VanceVagell/kv4p-ht/website-src/img/v1.7b-harmonics.jpg

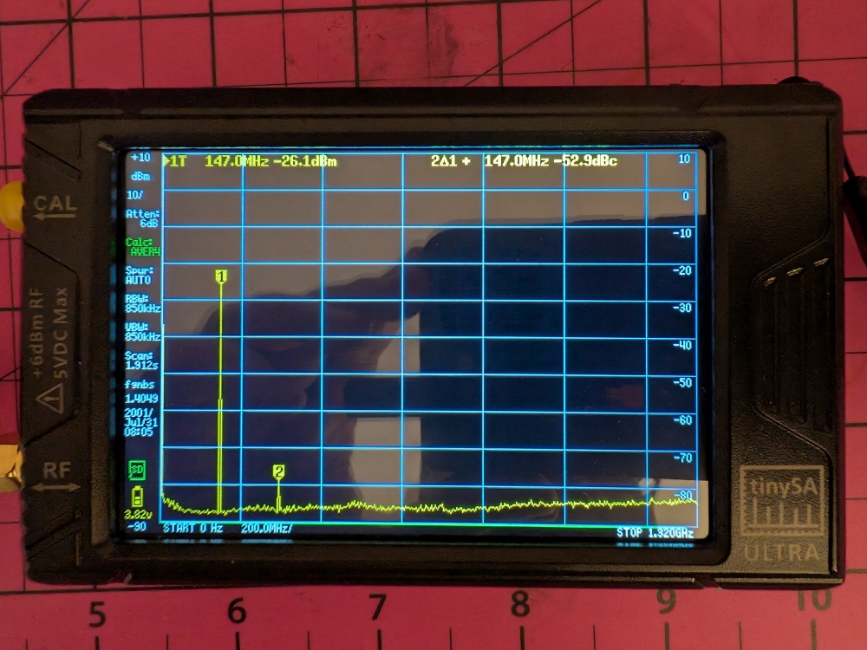
website-src/img/v1.7b-harmonics.jpg
