VanceVagell/kv4p-ht/3d-print-case/Cases for 2.x PCB/Sleek (official)/Sleek KV4P HT case (for PCB 2.x) - logo inlay.stl

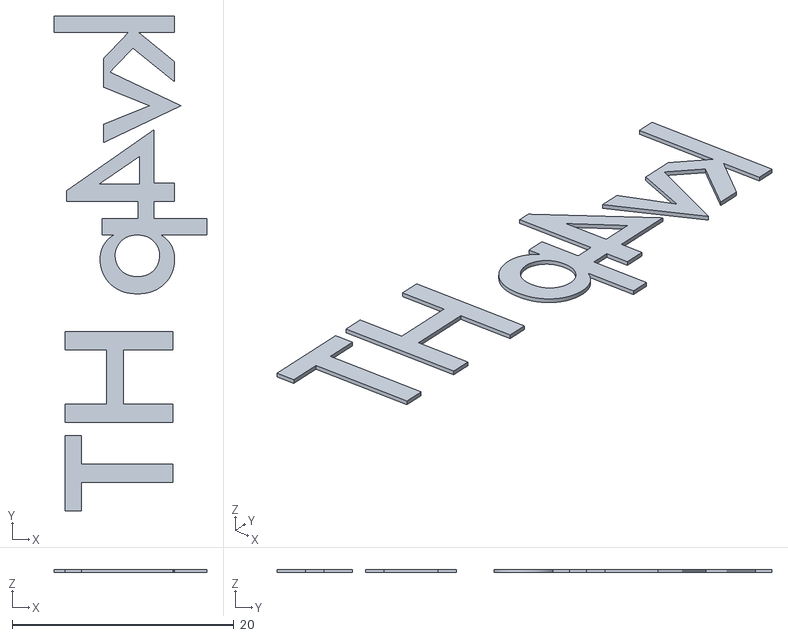
[picture p22: CAD file, 2026-09-27]
3d-print-case/Cases for 2.x PCB/Sleek (official)/Sleek KV4P HT case (for PCB 2.x) - logo inlay.stl
13.8 x 44.6 x 0.306
