VanceVagell/kv4p-ht/3d-print-case/Cases for 1.x PCB/alternate case designs/PCB slide-in case with stand/KV4P HT Stand.stl

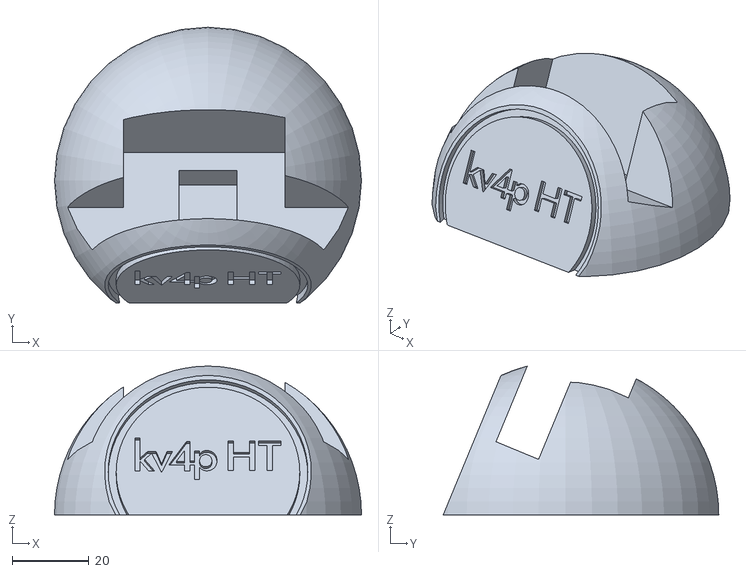
[picture p23: CAD file, 2024-06-17]
3d-print-case/Cases for 1.x PCB/alternate case designs/PCB slide-in case with stand/KV4P HT Stand.stl
80.0 x 71.8 x 38.7
