VanceVagell/kv4p-ht/3d-print-case/Cases for 2.x PCB/Community designs/KB9VQQ Design/Thin Case/kv4p-ThinCase-Body.stl

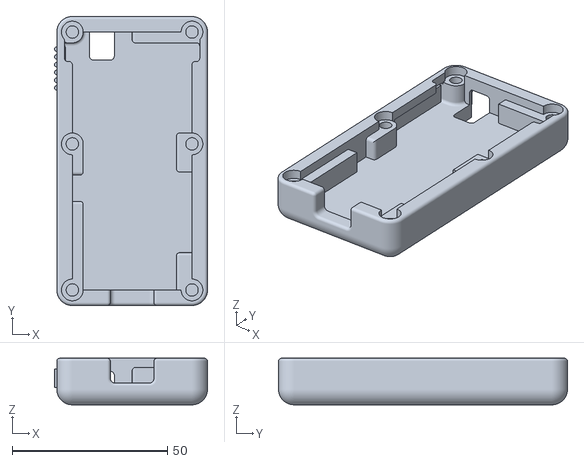
[picture p24: CAD file, 2025-10-06]
3d-print-case/Cases for 2.x PCB/Community designs/KB9VQQ Design/Thin Case/kv4p-ThinCase-Body.stl
49.2 x 93.0 x 15.0
