VanceVagell/kv4p-ht/3d-print-case/Cases for 2.x PCB/Rugged (official)/Rugged KV4P HT case (for PCB 2.x) - back.stl

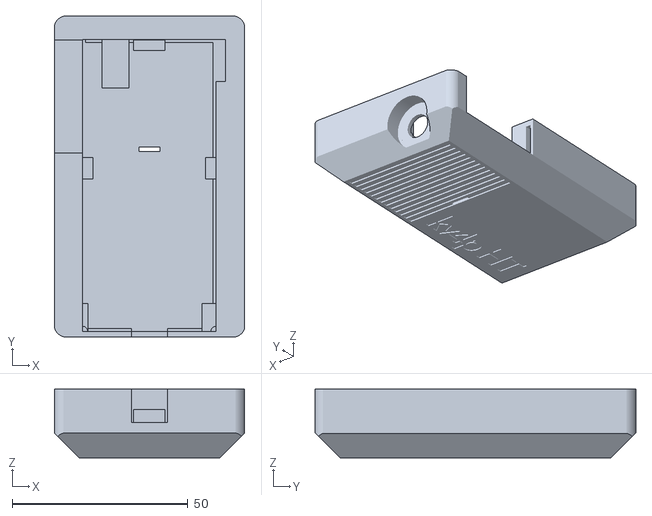
[picture p25: CAD file, 2026-09-27]
3d-print-case/Cases for 2.x PCB/Rugged (official)/Rugged KV4P HT case (for PCB 2.x) - back.stl
54.0 x 91.1 x 19.5
