VanceVagell/kv4p-ht/android-src/KV4PHT/app/src/main/java/com/vagell/kv4pht/radio/RadioAudioService.java

/*
kv4p HT (see http://kv4p.com)
Copyright (C) 2024 Vance Vagell

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
You should have received a copy of the GNU General Public License
along with this program.  If not, see <http://www.gnu.org/licenses/>.
*/

package com.vagell.kv4pht.radio;

import android.Manifest;
import android.app.Notification;
import android.app.NotificationChannel;
import android.app.NotificationManager;
import android.app.PendingIntent;
import android.app.Service;
import android.content.Context;
import android.content.Intent;
import android.content.pm.PackageManager;
import android.content.pm.ServiceInfo;
import android.hardware.usb.UsbDevice;
import android.hardware.usb.UsbDeviceConnection;
import android.hardware.usb.UsbManager;
import android.media.AudioAttributes;
import android.media.AudioFocusRequest;
import android.media.AudioFormat;
import android.media.AudioManager;
import android.media.AudioRecord;
import android.media.AudioTrack;
import android.media.MediaRecorder;
import android.os.Binder;
import android.os.Build;
import android.os.Bundle;
import android.os.Handler;
import android.os.IBinder;
import android.os.Looper;
import android.os.PowerManager;
import android.util.Log;
import androidx.annotation.NonNull;
import androidx.annotation.RequiresApi;
import androidx.annotation.RequiresPermission;
import androidx.core.app.NotificationCompat;
import androidx.lifecycle.LiveData;
import com.google.android.gms.common.ConnectionResult;
import com.google.android.gms.common.GoogleApiAvailability;
import com.google.android.gms.location.FusedLocationProviderClient;
import com.google.android.gms.location.LocationServices;
import com.google.android.gms.location.Priority;
import com.google.android.gms.tasks.CancellationToken;
import com.google.android.gms.tasks.CancellationTokenSource;
import com.hoho.android.usbserial.driver.UsbSerialDriver;
import com.hoho.android.usbserial.driver.UsbSerialPort;
import com.hoho.android.usbserial.driver.UsbSerialProber;
import com.vagell.kv4pht.BuildConfig;
import com.vagell.kv4pht.R;
import io.github.dkaukov.aprs.AprsController;
import io.github.dkaukov.aprs.BeaconData;
import io.github.dkaukov.aprs.AprsEvent;
import io.github.dkaukov.aprs.AprsIsClient;
import io.github.dkaukov.aprs.AprsSource;
import com.vagell.kv4pht.ui.APRSIconType;
import io.github.dkaukov.aprs.parser.APRSPacket;
import io.github.dkaukov.aprs.parser.Digipeater;
import io.github.dkaukov.aprs.parser.Parser;
import com.vagell.kv4pht.data.ChannelMemory;
import com.vagell.kv4pht.data.AprsFeedRepository;
import com.vagell.kv4pht.data.AprsFeedRow;
import com.vagell.kv4pht.data.AppDatabase;
import com.vagell.kv4pht.data.RoomAprsRepository;
import com.vagell.kv4pht.firmware.FirmwareUtils;
import com.vagell.kv4pht.javAX25.ax25.Packet;
import com.vagell.kv4pht.radio.Protocol.KissParser;
import com.vagell.kv4pht.radio.Protocol.RcvCommand;
import com.vagell.kv4pht.radio.Protocol.WindowUpdate;
import com.vagell.kv4pht.ui.MainActivity;
import com.vagell.kv4pht.ui.ToneHelper;
import io.github.dkaukov.codec2.Codec2;
import lombok.Getter;
import lombok.Setter;
import java.nio.ByteBuffer;
import java.nio.charset.StandardCharsets;
import java.util.Collections;
import java.util.List;
import java.util.Locale;
import java.util.Optional;
import java.util.concurrent.Executors;
import java.util.concurrent.ExecutorService;
import java.util.concurrent.ScheduledExecutorService;
import java.util.concurrent.TimeUnit;
import java.util.concurrent.atomic.AtomicInteger;
import java.util.concurrent.atomic.AtomicReference;

/**
 * Background service that manages the connection to the ESP32 (to control the radio), and
 * handles playing back any audio received from the radio. This frees up the rest of the
 * application to focus primarily on the setup flows and UI, and ensures that the radio audio
 * continues to play even if the phone's screen is off or the user starts another app.
 */
public class RadioAudioService extends Service {
    private static final String MEGAHERTZ = " MHz";
    private static final String MEMORY_FREQUENCY_SUFFIX = MEGAHERTZ + ")";
    private static final String SIMPLEX_PREFIX = "Simplex ";
    private static final String CURRENT_FREQUENCY = "Current";
    private static final String NOTIFICATION_CHANNEL_ID = "KV4P_HT_RADIO_AUDIO";

    // === Constants ===
    private static final String TAG = RadioAudioService.class.getSimpleName();
    private static final String FIRMWARE_TAG = "firmware";
    private static final String APRS_TOCALL = "APKVPA";
    private static final String ACTION_USB_PERMISSION = "com.vagell.kv4pht.USB_PERMISSION";
    private static final int RUNAWAY_TX_TIMEOUT_SEC = 180;
    // Intents this Activity can handle besides the one that starts it in default mode.
    public static final String INTENT_OPEN_CHAT = "com.vagell.kv4pht.OPEN_CHAT_ACTION";
    public static final String ACTION_STOP_SERVICE = "com.vagell.kv4pht.STOP_RADIO_SERVICE";
    public static final String ACTION_SERVICE_STOPPING = "com.vagell.kv4pht.SERVICE_STOPPING";


    // === USB Device Matching ===
    private static final int[] ESP32_VENDOR_IDS = {4292, 6790};
    private static final int[] ESP32_PRODUCT_IDS = {60000, 29987};

    // === Audio Constants ===
    public static final int AUDIO_SAMPLE_RATE = 16000;
    private static final int RX_AUDIO_CHANNEL_CONFIG = AudioFormat.CHANNEL_OUT_MONO;
    private static final int RX_AUDIO_FORMAT = AudioFormat.ENCODING_PCM_16BIT;
    public static final int AUDIO_FRAME_SAMPLES = 249; // One 128-byte mono IMA ADPCM audio block at 16kHz
    public static final int AUDIO_FRAME_BYTES = ImaAdpcm.encodedSize(AUDIO_FRAME_SAMPLES);
    private static final int RX_AUDIO_MIN_BUFFER_SIZE =
            Math.max(AudioTrack.getMinBufferSize(
                    AUDIO_SAMPLE_RATE,
                    RX_AUDIO_CHANNEL_CONFIG,
                    RX_AUDIO_FORMAT),
                    AUDIO_FRAME_SAMPLES * 2);

    // === APRS Constants ===
    public static final int APRS_POSITION_EXACT = 0;
    public static final int APRS_POSITION_APPROX = 1;
    public static final int APRS_BEACON_MINS = 5;
    public static final String MESSAGE_NOTIFICATION_CHANNEL_ID = "aprs_message_notifications";
    public static final int MESSAGE_NOTIFICATION_TO_YOU_ID = 0;
    public static final List<Digipeater> DEFAULT_DIGIPEATERS = List.of(new Digipeater("WIDE1-1"), new Digipeater("WIDE2-1"));
    private static final long SCAN_SQUELCHED_ADVANCE_DELAY_MS = 250L;

    // === Used for the persistent notification ===
    private PowerManager.WakeLock wakeLock;
    private static final int SERVICE_ID = 1;

    // These will be overwritten by user settings
    @Setter
    private float min2mTxFreq = 144.0f;
    @Setter
    private float max2mTxFreq = 148.0f;
    @Setter
    private float min70cmTxFreq = 420.0f;
    @Setter
    private float max70cmTxFreq = 450.0f;

    @Setter
    private float minTxFreq = min2mTxFreq;
    @Setter
    private float maxTxFreq = max2mTxFreq;

    @Setter
    private APRSIconType aprsPositionIcon = APRSIconType.T_PHONE;

    public enum RadioModuleType {UNKNOWN, VHF, UHF}

    // === Audio / 4-bit IMA ADPCM Handling ===
    private final short[] pcm16 = new short[AUDIO_FRAME_SAMPLES];
    private AudioTrack audioTrack;
    private float audioTrackVolume = 0.0f;
    private AudioFocusRequest audioFocusRequest;
    private boolean hasAudioFocus = false;
    private final byte[] txAudioFrame = new byte[AUDIO_FRAME_BYTES];
    private final ImaAdpcm.Encoder txAudioEncoder = new ImaAdpcm.Encoder();
    private Codec2 codec2;
    private boolean freeDv2400bEnabled;
    private final short[] codec2TxPcm = new short[Codec2.PCM_SAMPLES];
    private final short[] codec2RxPcm = new short[Codec2.PCM_SAMPLES];
    private final short[] codec2PlaybackPcm = new short[Codec2.PCM_SAMPLES * 2];
    private final byte[] codec2Frame = new byte[Codec2.FRAME_BYTES];
    private int codec2TxSamples;
    private boolean codec2HasPendingInput;
    private short codec2PendingInput;
    private final AtomicReference<AudioRecord> audioRecord = new AtomicReference<>();
    private volatile boolean voiceCaptureActive;
    private final AtomicInteger voiceCaptureSession = new AtomicInteger();
    private static final int TX_AUDIO_MIN_BUFFER_SIZE = Math.max(
            AudioRecord.getMinBufferSize(AUDIO_SAMPLE_RATE, AudioFormat.CHANNEL_IN_MONO,
                    AudioFormat.ENCODING_PCM_16BIT), AUDIO_FRAME_SAMPLES * 2);

    // === USB / Serial ===
    private UsbManager usbManager;
    private RadioTransport activeTransport;
    private boolean usbPermissionRequestPending = false;
    @Getter
    private Protocol.Sender hostToEsp32;
    @Getter
    private final RadioModuleController radioModule = new RadioModuleController();
    private final KissParser esp32DataStreamParser = new KissParser(this::handleParsedCommand, this::handleEsp32Ax25Packet);
    private int usbConnectAttemptSeq = 0;
    private int activeUsbConnectAttemptId = 0;

    // === APRS State ===
    private String aprsBeaconFrequency = CURRENT_FREQUENCY;
    // Confined to the ordered APRS worker while submitting one app-scheduled beacon.
    private Float aprsBeaconTxOverrideMhz;
    @Getter
    @Setter
    private int aprsPositionAccuracy = APRS_POSITION_EXACT;
    private AprsIsClient aprsIsClient;
    private boolean aprsIgateEnabled;
    private boolean aprsIsDisplayEnabled;

    // === Protocol Handshake ===
    private static final int HELLO_TIMEOUT_MS = 60000;
    private int handshakeSeq = 0;
    private int activeHandshakeId = 0;
    private boolean waitingForHello = false;
    private Runnable helloTimeoutRunnable;

    // === Radio State ===
    @Getter
    private @NonNull RadioMode mode = RadioMode.STARTUP;
    private @NonNull String callsign = "";
    @Getter
    private @NonNull String activeFrequencyStr = "";
    private int activeMemoryId = -1;
    private int scanBaseSquelch = -1;
    private static final int DEFAULT_SCAN_SQUELCH = 7;
    private Runnable pendingScanAdvance;
    private int pendingScanAdvanceMemoryId = -1;
    private MicGainBoost micGainBoost = MicGainBoost.NONE;

    // === Android Components ===
    private final IBinder binder = new RadioBinder();
    private static final RadioAudioServiceCallbacks NO_OP_CALLBACKS = new RadioAudioServiceCallbacks() {};
    @Setter
    @Getter
    private @NonNull RadioAudioServiceCallbacks callbacks = NO_OP_CALLBACKS;
    private final Handler handler = new Handler(Looper.getMainLooper());
    private static final long CONNECT_RETRY_PERIOD_MS = 500L;
    private final ConnectionController connectionController =
        new ConnectionController(handler, CONNECT_RETRY_PERIOD_MS, this::reconcileConnections);
    private boolean radioMissingNotified = false;
    private Runnable txTimeoutHandler;
    private LiveData<List<ChannelMemory>> channelMemoriesLiveData = null;
    private ScheduledExecutorService aprsExecutor;
    private volatile boolean aprsBeaconPosition;
    // Main-handler-owned scheduling preserves GPS and alternate-frequency beaconing.
    private final AprsBeaconSchedule aprsBeaconSchedule = new AprsBeaconSchedule(APRS_BEACON_MINS * 60_000L);
    private AprsController aprsController;
    private AprsFeedRepository aprsFeedRepository;

    /**
     * Class used for the client Binder. This service always runs in the same process as its clients.
     */
    public class RadioBinder extends Binder {
        public RadioAudioService getService() {
            // Return this instance of RadioService so clients can call public methods.
            return RadioAudioService.this;
        }
    }

    /**
     * Callbacks for the activity to implement, so it can be notified of various events.
     */
    public interface RadioAudioServiceCallbacks {
        default void radioMissing() {}
        default void radioConnected() {}
        default void hideSnackBar() {}
        default void radioModuleHandshake() {}
        default void radioModuleNotFound() {}
        default void audioTrackCreated() {}
        default void startingAprsBeacon(String frequencyStr) {}
        default void scannedToMemory(int memoryId) {}
        default void tunedToFreq(String frequencyStr) {}
        default void outdatedFirmware(int firmwareVer) {}
        default void initialDeviceStateReceived() {}
        default void radioConfigChanged() {}
        default void missingFirmware() {}
        default void txStarted() {}
        default void txEnded() {}
        default void moduleStateChanged(boolean txActive, boolean squelched) {}
        default void freeDvModeChanged(boolean enabled) {}
        default void chatError(String text) {}
        default void sMeterUpdate(int value) {}
        default void sentAprsBeacon(double latitude, double longitude, String frequencyStr, boolean wasSwitch) {}
        default void unknownLocation() {}
        default void forcedPttStart() {}
        default void forcedPttEnd() {}
        default void setRadioType(RadioModuleType ratioType) {}
        default void showNotification(String notificationChannelId, int notificationTypeId, String title, String message, String tapIntentName) {}
    }

    @Override
    public IBinder onBind(Intent intent) {
        Bundle bundle = intent.getExtras();
        if (null == bundle) {
            Log.d(TAG, "Warning: RadioAudioService started without parameters, likely in a bad state.");
            return binder;
        }

        // Retrieve necessary parameters from the intent.
        setCallsign(Optional.ofNullable(bundle.getString("callsign")).orElse(""));
        if (bundle.containsKey("squelch")) {
            radioModule.seedDesiredSquelch(bundle.getInt("squelch"));
        }
        activeMemoryId = bundle.getInt("activeMemoryId");
        activeFrequencyStr = Optional.ofNullable(bundle.getString("activeFrequencyStr")).orElse("");
        return binder;
    }

    public void setMicGainBoost(String micGainBoost) {
        this.micGainBoost = MicGainBoost.parse(micGainBoost);
    }

    public void setAprsBeaconPosition(boolean enabled) {
        aprsBeaconPosition = enabled;
        handler.post(() -> aprsBeaconSchedule.setEnabled(enabled));
    }

    public void setAprsBeaconFrequency(String frequency) {
        this.aprsBeaconFrequency = frequency;
    }

    public void setDigipeatPackets(boolean enabled) {
        executeAprs(() -> aprsController.setDigipeatingEnabled(enabled));
    }

    public void setAprsIgateEnabled(boolean enabled) {
        aprsIgateEnabled = enabled;
        executeAprs(() -> aprsController.setIgateEnabled(enabled));
        updateAprsIsConnection();
    }

    public void setAprsIsDisplayEnabled(boolean enabled) {
        aprsIsDisplayEnabled = enabled;
        AprsIsClient client = aprsIsClient;
        if (client != null) client.setReceiveEnabled(enabled);
        if (enabled) refreshAprsIsFilterLocation();
        else if (client != null) client.setFilterLocation(null, null);
        updateAprsIsConnection();
    }

    public void setCallsign(@NonNull String callsign) {
        this.callsign = callsign;
        if (aprsController != null) executeAprs(() -> aprsController.setCallsign(callsign));
        if (aprsFeedRepository != null) aprsFeedRepository.refresh();
        AprsIsClient client = aprsIsClient;
        if (client != null) client.setCallsign(callsign);
    }

    private void updateAprsIsConnection() {
        AprsIsClient client = aprsIsClient;
        if (client == null) return;
        client.setCallsign(callsign);
        boolean active = aprsIgateEnabled || aprsIsDisplayEnabled;
        if (!active) {
            client.setEnabled(false);
            client.setTransmitEnabled(false);
            return;
        }
        client.setTransmitEnabled(aprsIgateEnabled);
        client.setEnabled(true);
    }

    private void refreshAprsIsFilterLocation() {
        AprsIsClient client = aprsIsClient;
        if (client == null) return;
        client.setFilterLocation(null, null);
        if (checkSelfPermission(Manifest.permission.ACCESS_FINE_LOCATION)
                    != PackageManager.PERMISSION_GRANTED
                && checkSelfPermission(Manifest.permission.ACCESS_COARSE_LOCATION)
                    != PackageManager.PERMISSION_GRANTED) return;
        if (GoogleApiAvailability.getInstance().isGooglePlayServicesAvailable(getBaseContext())
                != ConnectionResult.SUCCESS) return;
        FusedLocationProviderClient locationClient =
            LocationServices.getFusedLocationProviderClient(this);
        CancellationToken token = new CancellationTokenSource().getToken();
        locationClient.getCurrentLocation(Priority.PRIORITY_BALANCED_POWER_ACCURACY, token)
            .addOnSuccessListener(location -> {
                if (aprsIsDisplayEnabled && location != null) {
                    updateAprsIsFilterLocation(location.getLatitude(), location.getLongitude());
                }
            });
    }

    private void updateAprsIsFilterLocation(double latitude, double longitude) {
        AprsIsClient client = aprsIsClient;
        if (client != null && aprsIsDisplayEnabled) {
            client.setFilterLocation(latitude, longitude);
        }
    }

    public void setAprsHistoryWindow(String historyWindow) {
        aprsFeedRepository.setHistoryWindow(historyWindow);
    }

    public void setAprsDestinationFilter(String destinationFilter) {
        aprsFeedRepository.setDestinationFilter(destinationFilter);
    }

    public boolean getAprsBeaconPosition() {
        return aprsBeaconPosition;
    }

    public void setMode(RadioMode mode) {
        if (mode == RadioMode.FLASHING) {
            if (!canFlashFirmware()) {
                Log.w(TAG, "Firmware flashing requires USB serial; current transport is not flash-capable.");
                return;
            }
            radioModule.stop();
            audioTrack.stop();
            if (!activeTransport.prepareForFirmwareFlashing()) {
                Log.w(TAG, "USB transport could not enter firmware flashing mode.");
                return;
            }
        }

        RadioMode previousMode = this.mode;
        this.mode = mode;
        if (previousMode != mode) {
            syncFirmwareAudioStateForMode(mode);
            if ((mode == RadioMode.RX || mode == RadioMode.SCAN) && radioModule.hasRadioConfig()) {
                updateAudioFocusForSquelch(radioModule.isSquelched());
            } else {
                abandonAudioFocus();
            }
        }
    }

    private void syncFirmwareAudioStateForMode(RadioMode mode) {
        if (!isConnectionReady()) {
            return;
        }
        if (mode == RadioMode.RX || mode == RadioMode.SCAN) {
            openFirmwareAudio();
        } else if (mode == RadioMode.STARTUP || mode == RadioMode.BAD_FIRMWARE || mode == RadioMode.UNKNOWN) {
            radioModule.closeAudio();
        }
    }

    void openFirmwareAudio() {
        if (isConnectionReady()) {
            radioModule.openAudio();
        }
    }

    public void setActiveMemoryId(int activeMemoryId) {
        this.activeMemoryId = activeMemoryId;
        if (activeMemoryId > -1) {
            tuneToMemory(activeMemoryId);
        } else {
            tuneToFreq(activeFrequencyStr);
        }
    }

    public LiveData<List<AprsFeedRow>> getAprsFeed() {
        return aprsFeedRepository.getFeed();
    }

    @Override
    public void onCreate() {
        super.onCreate();
        aprsExecutor = Executors.newSingleThreadScheduledExecutor();
        aprsController = createAprsController();
        aprsIsClient = new AprsIsClient("kv4p-ht", BuildConfig.VERSION_NAME,
            packet -> executeAprs(() -> aprsController.handleAprsIsPacket(packet)));
        aprsIsClient.setServer("rotate.aprs2.net:14580");

        // Keep CPU on while service is running so we can play and process audio
        PowerManager pm = (PowerManager) getSystemService(POWER_SERVICE);
        wakeLock = pm.newWakeLock(PowerManager.PARTIAL_WAKE_LOCK,
                "RadioAudioService::Playback");
        wakeLock.setReferenceCounted(false);

        // Create channel for the persistent notification user can interact with
        if (Build.VERSION.SDK_INT >= Build.VERSION_CODES.O) {
            NotificationChannel chan = new NotificationChannel(
                    NOTIFICATION_CHANNEL_ID,
                    "kv4p HT audio",
                    NotificationManager.IMPORTANCE_DEFAULT);
            chan.setSound(null, null); // no sound for the notification itself
            chan.setShowBadge(false);

            NotificationManager nm = getSystemService(NotificationManager.class);
            nm.createNotificationChannel(chan);
        }
        // Missed ticks do not accumulate: wait after each execution on the ordered APRS worker.
        aprsExecutor.scheduleWithFixedDelay(this::tickAprsController, 0, 500, TimeUnit.MILLISECONDS);
    }

    private void tickAprsController() {
        try {
            aprsController.tick(System.currentTimeMillis());
        } catch (RuntimeException e) {
            // Unhandled exceptions cancel future executions of a scheduled periodic task.
            Log.w(TAG, "APRS housekeeping tick failed; later ticks remain scheduled", e);
        }
    }

    private AprsController createAprsController() {
        AppDatabase database = AppDatabase.getInstance(getApplicationContext());
        aprsFeedRepository = new AprsFeedRepository(database.aprsEventDao(), aprsExecutor,
            () -> callsign);
        AprsController controller = new AprsController(
            new RoomAprsRepository(database, aprsFeedRepository), new ServiceAprsCallbacks());
        controller.setCallsign(callsign);
        controller.setTxDestination(APRS_TOCALL);
        controller.setTxPath(DEFAULT_DIGIPEATERS);
        return controller;
    }

    /** Keeps synchronous controller storage off UI/transport threads and preserves arrival order. */
    private void executeAprs(Runnable operation) {
        ExecutorService executor = aprsExecutor;
        if (executor == null) return;
        try {
            executor.execute(operation);
        } catch (java.util.concurrent.RejectedExecutionException e) {
            Log.d(TAG, "Ignoring APRS work after service shutdown", e);
        }
    }

    /** Uses the existing connection tick; GPS and frequency switching stay asynchronous. */
    private void tickPositionBeacon() {
        long now = System.currentTimeMillis();
        if (!aprsBeaconSchedule.isDue(now)) return;
        if (checkSelfPermission(Manifest.permission.ACCESS_FINE_LOCATION)
                != PackageManager.PERMISSION_GRANTED
                || checkSelfPermission(Manifest.permission.ACCESS_COARSE_LOCATION)
                != PackageManager.PERMISSION_GRANTED) {
            callbacks.unknownLocation();
            return;
        }
        try {
            if (wakeLock != null && !wakeLock.isHeld()) wakeLock.acquire(20_000);
            sendPositionBeacon();
        } finally {
            if (wakeLock != null && wakeLock.isHeld()) wakeLock.release();
        }
    }

    private final class ServiceAprsCallbacks implements AprsController.Callbacks {
        @Override public void onIncomingMessage(AprsEvent event, boolean forLocal) {
            if (!forLocal) return;
            handler.post(() -> callbacks.showNotification(MESSAGE_NOTIFICATION_CHANNEL_ID,
                MESSAGE_NOTIFICATION_TO_YOU_ID, event.getFromCallsign() + " messaged you",
                event.getBody(), INTENT_OPEN_CHAT));
        }

        @Override public AprsController.RfTransmission submitRf(APRSPacket packet, Long requestedFrequencyHz,
                AprsController.RfTransmissionPurpose purpose) {
            if (!canTransmitAprs()) {
                return null;
            }
            Long selectedTxHz = activeTxFrequencyHz();
            if (AprsRfFrequencyPolicy.isTerminalMismatch(requestedFrequencyHz, selectedTxHz, purpose)) {
                Log.d(TAG, "Rejecting APRS RF submission: requested " + requestedFrequencyHz
                    + " Hz, selected TX frequency " + selectedTxHz + " Hz, purpose " + purpose);
                // The app does not automatically retune to the original message frequency.
                return AprsController.RfTransmission.builder().retryAllowed(false).build();
            }
            Long targetHz = requestedFrequencyHz;
            if (purpose == AprsController.RfTransmissionPurpose.POSITION_BEACON
                    && aprsBeaconTxOverrideMhz != null) {
                targetHz = AprsRfFrequencyPolicy.toHz(aprsBeaconTxOverrideMhz);
            }
            Long frequencyHz = AprsRfFrequencyPolicy.transmissionFrequency(targetHz, selectedTxHz, purpose);
            if (frequencyHz == null) return null;
            AprsController.Transmission transmission = transmitAprsPacketOnFrequency(packet,
                frequencyHz, (float) (frequencyHz / 1_000_000d));
            return AprsController.RfTransmission.builder().transmission(transmission).build();
        }

        @Override public BeaconData getBeaconData() {
            // Beacon scheduling is app-owned: location and frequency changes are asynchronous.
            return null;
        }

        @Override public boolean submitAprsIs(String tnc2, Runnable onSuccess) {
            AprsIsClient client = aprsIsClient;
            return client != null && client.send(callsign, tnc2,
                () -> executeAprs(onSuccess));
        }

        private boolean canTransmitAprs() {
            return isTxAllowed() && AprsRfFrequencyPolicy.allowsMode(getMode())
                && hostToEsp32 != null;
        }

        private AprsController.Transmission transmitAprsPacketOnFrequency(
            APRSPacket packet, Long frequencyHz, float txFrequencyMhz) {
            byte[] rawAx25 = packet.toAX25Frame();
            return txAX25PacketOnFrequency(new Packet(rawAx25), txFrequencyMhz)
                ? AprsController.Transmission.builder().packet(packet).frequencyHz(frequencyHz)
                    .rawAx25(rawAx25).build() : null;
        }
    }

    /**
     * Bound activities should call this when they're done providing any data (via setters), including the several
     * necessary callback handlers.
     */
    public void start() {
        usbManager = (UsbManager) getSystemService(Context.USB_SERVICE);
        createNotificationChannels();
        initAudioTrack();
        connectionController.start();
    }

    @Override
    public int onStartCommand(Intent intent, int flags, int startId) {
        if (intent != null && ACTION_STOP_SERVICE.equals(intent.getAction())) {
            Intent stopIntent = new Intent(ACTION_SERVICE_STOPPING);
            stopIntent.setPackage(getPackageName());
            sendBroadcast(stopIntent); // NOSONAR S5320: package-scoped and received only by this app.
            stopForeground(STOP_FOREGROUND_REMOVE);
            stopSelf();
            return START_NOT_STICKY;
        }

        Notification notification = buildForegroundNotification();

        try {
            if (Build.VERSION.SDK_INT >= Build.VERSION_CODES.R) {
                startForeground(
                        SERVICE_ID,
                        notification,
                        ServiceInfo.FOREGROUND_SERVICE_TYPE_LOCATION
                                | ServiceInfo.FOREGROUND_SERVICE_TYPE_MEDIA_PLAYBACK
                                | ServiceInfo.FOREGROUND_SERVICE_TYPE_MICROPHONE
                );
            } else if (Build.VERSION.SDK_INT >= Build.VERSION_CODES.Q) {
                startForeground(
                        SERVICE_ID,
                        notification,
                        ServiceInfo.FOREGROUND_SERVICE_TYPE_LOCATION
                                | ServiceInfo.FOREGROUND_SERVICE_TYPE_MEDIA_PLAYBACK
                );
            } else {
                startForeground(SERVICE_ID, notification);
            }
        } catch (SecurityException e) {
            Log.e(TAG, "Unable to start foreground radio service.", e);
            stopSelf();
            return START_NOT_STICKY;
        }

        // Make the service sticky so it is restarted if the process dies
        return START_STICKY;
    }

    @RequiresApi(api = Build.VERSION_CODES.O)
    private Notification buildForegroundNotification() {
        Intent openApp = new Intent(this, MainActivity.class);
        PendingIntent pi = PendingIntent.getActivity(
                this, 0, openApp, PendingIntent.FLAG_IMMUTABLE);

        // Create an Intent that will be sent when the user swipes the notification away.
        Intent stopSelf = new Intent(this, RadioAudioService.class);
        stopSelf.setAction(ACTION_STOP_SERVICE);
        PendingIntent pStopSelf = PendingIntent.getService(this, 0, stopSelf, PendingIntent.FLAG_CANCEL_CURRENT | PendingIntent.FLAG_IMMUTABLE);

        return new NotificationCompat.Builder(this, NOTIFICATION_CHANNEL_ID)
                .setSmallIcon(R.drawable.ic_radio)
                .setContentTitle("kv4p HT")
                .setContentText("Starting up...")
                .setContentIntent(pi)
                .setDeleteIntent(pStopSelf)
                .setOngoing(true)
                .setOnlyAlertOnce(true)
                .setVisibility(NotificationCompat.VISIBILITY_PUBLIC) // visible on lock screen
                .build();
    }

    private void updateForegroundNotification(String text) {
        // Create an Intent that will be sent when the user swipes the notification away.
        Intent stopSelf = new Intent(this, RadioAudioService.class);
        stopSelf.setAction(ACTION_STOP_SERVICE);
        PendingIntent pStopSelf = PendingIntent.getService(this, 0, stopSelf, PendingIntent.FLAG_CANCEL_CURRENT | PendingIntent.FLAG_IMMUTABLE);

        Notification notification = new NotificationCompat.Builder(this, NOTIFICATION_CHANNEL_ID)
                .setSmallIcon(R.drawable.ic_radio)
                .setContentTitle("kv4p HT")
                .setContentText(text)
                .setContentIntent(buildPendingIntent())
                .setDeleteIntent(pStopSelf)
                .setOngoing(true)
                .setOnlyAlertOnce(true)
                .setVisibility(NotificationCompat.VISIBILITY_PUBLIC) // visible on lock screen
                .build();

        NotificationManager nm = (NotificationManager) getSystemService(NOTIFICATION_SERVICE);
        nm.notify(SERVICE_ID, notification);
    }

    private PendingIntent buildPendingIntent() {
        Intent open = new Intent(this, MainActivity.class);
        return PendingIntent.getActivity(this, 0, open,
                PendingIntent.FLAG_IMMUTABLE);
    }

    /**
     * This must be set before any method that requires channels (like scanning or tuning to a memory) is access, or
     * they will just report an error. And it should also be called whenever the active memories have changed (e.g.
     * user selected a different memory group).
     */
    public void setChannelMemories(LiveData<List<ChannelMemory>> channelMemoriesLiveData) {
        this.channelMemoriesLiveData = channelMemoriesLiveData;
    }

    /**
     * Updates the foreground notification with the current radio state (frequency or memory).
     * This is useful to call after initial connection or when memory definitions change.
     */
    public void updateNotificationFromCurrentState() {
        String text = notificationTextForActiveMemory();
        if (text == null) {
            text = notificationTextForSimplexFrequency();
        }
        if (text != null) {
            updateForegroundNotification(text);
        }
    }

    private String notificationTextForActiveMemory() {
        if (activeMemoryId > -1) {
            List<ChannelMemory> memories = channelMemoriesLiveData == null
                    ? null : channelMemoriesLiveData.getValue();
            if (memories != null) {
                for (ChannelMemory memory : memories) {
                    if (memory.memoryId == activeMemoryId) {
                        return memory.name + " (" + memory.frequency + MEMORY_FREQUENCY_SUFFIX;
                    }
                }
            }
            if (!activeFrequencyStr.isEmpty()) {
                return "Memory " + activeMemoryId + " (" + activeFrequencyStr + MEMORY_FREQUENCY_SUFFIX;
            }
        }
        return null;
    }

    private String notificationTextForSimplexFrequency() {
        if (activeMemoryId == -1 && !activeFrequencyStr.isEmpty()) {
            try {
                float freq = Float.parseFloat(activeFrequencyStr);
                return SIMPLEX_PREFIX + formatFreq(freq) + MEGAHERTZ;
            } catch (NumberFormatException e) {
                return SIMPLEX_PREFIX + activeFrequencyStr + MEGAHERTZ;
            }
        }
        return null;
    }

    @Override
    public void onDestroy() {
        super.onDestroy();
        tryToStopRadioModule();
        connectionController.stop();
        if (aprsIsClient != null) {
            aprsIsClient.close();
            aprsIsClient = null;
        }
        if (aprsExecutor != null) {
            aprsExecutor.shutdownNow();
        }
        cancelHelloTimeout();

        closePortAndReset();

        if (audioTrack != null) {
            audioTrack.stop();
            audioTrack.release();
            audioTrack = null;
        }
        if (codec2 != null) {
            codec2.close();
            codec2 = null;
        }
        abandonAudioFocus();
        stopVoiceCapture();

        if (wakeLock != null && wakeLock.isHeld()) {
            wakeLock.release();
        }
        wakeLock = null;
        stopForeground(STOP_FOREGROUND_REMOVE);
    }

    private void tryToStopRadioModule() {
        if (isConnectionReady() && (mode == RadioMode.RX || mode == RadioMode.TX || mode == RadioMode.SCAN)) {
            try {
                Log.d(TAG, "Sending stop to ESP32...");
                radioModule.closeAudio();
                Thread.sleep(100);
            } catch (InterruptedException e) {
                Thread.currentThread().interrupt();
            } catch (Exception ignored) {
                // Ignore, we are shutting down anyway.
            }
        }
    }

    @Override
    public void onTaskRemoved(Intent rootIntent) {
        super.onTaskRemoved(rootIntent);
        stopSelf();
    }

    private void createNotificationChannels() {
        // Notification channel for APRS text chat messages
        NotificationChannel channel = new NotificationChannel(MESSAGE_NOTIFICATION_CHANNEL_ID,
            "Chat messages", NotificationManager.IMPORTANCE_DEFAULT);
        channel.setDescription("APRS text chat messages addressed to you");
        NotificationManager notificationManager = getSystemService(NotificationManager.class);
        notificationManager.createNotificationChannel(channel);
    }

    /**
     * Determines if transmission (TX) is allowed on the given frequency.
     *
     * @param freq The frequency to check, in MHz.
     * @return true if the frequency is within the allowed transmission range, false otherwise.
     */
    private boolean canTransmitOnFrequency(float freq) {
        final float halfBandwidth = radioModule.getHalfBandwidthMhz();
        return  (freq >= (minTxFreq + halfBandwidth)) && (freq <= (maxTxFreq - halfBandwidth));
    }

    private void updateTxAllowed(float txFrequency) {
        radioModule.setTxAllowed(canTransmitOnFrequency(txFrequency));
    }

    public boolean isTxAllowed() {
        return radioModule.isTxAllowed();
    }

    public void tuneToFreq(String frequencyStr) {
        if (mode == RadioMode.STARTUP) {
            return; // Not fully loaded and initialized yet, don't tune.
        }
        setMode(RadioMode.RX);
        float freq;
        try {
            freq = Float.parseFloat(makeSafeHamFreq(frequencyStr));
            updateForegroundNotification(SIMPLEX_PREFIX + String.format(Locale.US, "%.4f", freq) + MEGAHERTZ);
        } catch (NumberFormatException e) {
            Log.w(TAG, "Invalid frequency string: " + frequencyStr, e);
            return;
        }
        activeFrequencyStr = frequencyStr;
        activeMemoryId = -1; // Reset active memory ID since we're tuning to a frequency, not a memory.
        callbacks.tunedToFreq(activeFrequencyStr);
        radioModule.beginUpdate();
        try {
            radioModule.setMemoryId(-1);
            radioModule.setTxFrequency(freq);
            radioModule.setRxFrequency(freq);
            radioModule.setTxTone((byte) 0);
            radioModule.setRxTone((byte) 0);
            updateTxAllowed(freq);
        } finally {
            radioModule.endUpdate();
        }
    }

    public String makeSafeHamFreq(String strFreq) {
        try {
            float freq = Float.parseFloat(strFreq);
            // Normalize values like "1467" → "146.7"
            while (freq > 500.0f) {
                freq /= 10;
            }
            return formatFreq(Math.max(getMinRadioFreq(), Math.min(freq, getMaxRadioFreq())));
        } catch (NumberFormatException e) {
            return formatFreq(minTxFreq);
        }
    }

    private static String formatFreq(float freq) {
        return String.format(java.util.Locale.US, "%.4f", freq);
    }

    public String validateFrequency(String tempFrequency) {
        // Resort to the old frequency, the one the user inputted is unsalvageable.
        return makeSafeHamFreq(tempFrequency);
    }

    public void tuneToMemory(int memoryId) {
        Optional.ofNullable(channelMemoriesLiveData)
            .map(LiveData::getValue)
            .orElse(Collections.emptyList())
            .stream()
            .filter(channelMemory -> channelMemory.memoryId == memoryId)
            .findFirst()
            .ifPresent(this::tuneToMemory);
    }

    public void tuneToMemory(ChannelMemory memory) {
        if (memory == null || mode == RadioMode.STARTUP) {
            return;
        }
        activeFrequencyStr = validateFrequency(memory.frequency);
        activeMemoryId = memory.memoryId;
        final float txFreq = Float.parseFloat(getTxFreq(memory.frequency, memory.offset, memory.offsetKhz));
        radioModule.beginUpdate();
        try {
            radioModule.setMemoryId(memory.memoryId);
            radioModule.setTxFrequency(txFreq);
            radioModule.setRxFrequency(Float.parseFloat(makeSafeHamFreq(activeFrequencyStr)));
            radioModule.setTxTone((byte) Math.max(0, ToneHelper.getToneIndex(memory.txTone)));
            radioModule.setRxTone((byte) Math.max(0, ToneHelper.getToneIndex(memory.rxTone)));
            updateTxAllowed(txFreq);
        } finally {
            radioModule.endUpdate();
        }
        updateForegroundNotification(memory.name + " (" + memory.frequency + " MHz)");
        callbacks.scannedToMemory(memory.memoryId);
    }

    private String getTxFreq(String txFreq, int offset, int khz) {
        if (offset == ChannelMemory.OFFSET_NONE) {
            return txFreq;
        } else {
            float freqFloat = Float.parseFloat(txFreq);
            if (offset == ChannelMemory.OFFSET_UP) {
                freqFloat += 0f + (khz / 1000f);
            } else if (offset == ChannelMemory.OFFSET_DOWN) {
                freqFloat -= 0f + (khz / 1000f);
            }
            return makeSafeHamFreq(Float.toString(freqFloat));
        }
    }

    private void checkScanDueToSquelch() {
        if (getMode() != RadioMode.SCAN) {
            cancelPendingScanAdvance();
            return;
        }
        if (radioModule.getMemoryId() == activeMemoryId && radioModule.isSquelched()) {
            scheduleScanAdvance(activeMemoryId);
        } else {
            cancelPendingScanAdvance();
        }
    }

    private void scheduleScanAdvance(int memoryId) {
        if (pendingScanAdvance != null && pendingScanAdvanceMemoryId == memoryId) {
            return;
        }
        cancelPendingScanAdvance();
        pendingScanAdvanceMemoryId = memoryId;
        pendingScanAdvance = () -> {
            pendingScanAdvance = null;
            pendingScanAdvanceMemoryId = -1;
            if (getMode() == RadioMode.SCAN
                && activeMemoryId == memoryId
                && radioModule.getMemoryId() == memoryId
                && radioModule.isSquelched()) {
                nextScan();
            }
        };
        handler.postDelayed(pendingScanAdvance, SCAN_SQUELCHED_ADVANCE_DELAY_MS);
    }

    private void cancelPendingScanAdvance() {
        if (pendingScanAdvance != null) {
            handler.removeCallbacks(pendingScanAdvance);
            pendingScanAdvance = null;
            pendingScanAdvanceMemoryId = -1;
        }
    }

    private void initAudioTrack() {
        if (audioTrack != null) {
            audioTrack.release();
            audioTrack = null;
        }
        AudioAttributes audioAttributes = new AudioAttributes.Builder()
            .setUsage(AudioAttributes.USAGE_MEDIA)
            .setContentType(AudioAttributes.CONTENT_TYPE_SPEECH)
            .build();
        audioFocusRequest = new AudioFocusRequest.Builder(AudioManager.AUDIOFOCUS_GAIN_TRANSIENT)
            .setAudioAttributes(audioAttributes)
            .build();
        audioTrack = new AudioTrack.Builder()
            .setAudioAttributes(audioAttributes)
            .setAudioFormat(new AudioFormat.Builder()
                .setEncoding(RX_AUDIO_FORMAT)
                .setSampleRate(AUDIO_SAMPLE_RATE)
                .setChannelMask(AudioFormat.CHANNEL_OUT_MONO)
                .build())
            .setTransferMode(AudioTrack.MODE_STREAM)
            .setBufferSizeInBytes(RX_AUDIO_MIN_BUFFER_SIZE)
            .setPerformanceMode(AudioTrack.PERFORMANCE_MODE_LOW_LATENCY)
            .build();
        audioTrack.setVolume(0.0f);
        audioTrackVolume = 0.0f;
        audioTrack.setAuxEffectSendLevel(0.0f);
        callbacks.audioTrackCreated();
    }

    private void setTxRunAwayTimer() {
        // cancel any existing timeout
        if (txTimeoutHandler != null) {
            handler.removeCallbacks(txTimeoutHandler);
        }
        txTimeoutHandler = () -> {
            if (RadioMode.TX.equals(getMode())) {
                Log.d(TAG, "Warning: runaway TX timeout reached, PTT stopped.");
                endPtt();
            }
        };
        handler.postDelayed(txTimeoutHandler, RUNAWAY_TX_TIMEOUT_SEC * 1000L);
    }

    public void startPtt() {
        if (hostToEsp32 == null) {
            Log.e(TAG, "Attempted to start PTT but hostToEsp32 is null. USB connection likely failed.");
            radioMissing();
            return;
        }
        if (mode == RadioMode.RX && isTxAllowed()) {
            txAudioEncoder.reset();
            codec2TxSamples = 0;
            codec2HasPendingInput = false;
            setMode(RadioMode.TX);
            callbacks.sMeterUpdate(0);
            setTxRunAwayTimer();
            radioModule.pttDown();
            audioTrackVolume = 0.0f;
            Optional.ofNullable(audioTrack).ifPresent(t -> t.setVolume(0.0f));
            startVoiceCapture();
            callbacks.txStarted();
        } else {
            Log.w(TAG, "Attempted to start PTT when not allowed", new Throwable());
        }
    }

    public void endPtt() {
        if (mode == RadioMode.TX) {
            stopVoiceCapture();
            setMode(RadioMode.RX);
            audioTrackVolume = 0.0f;
            Optional.ofNullable(audioTrack).ifPresent(t -> t.setVolume(0.0f));
            radioModule.pttUp();
            callbacks.txEnded();
        }
    }

    public boolean isVoiceCaptureActive() {
        return voiceCaptureActive;
    }

    private void startVoiceCapture() {
        if (voiceCaptureActive || checkSelfPermission(Manifest.permission.RECORD_AUDIO)
                != PackageManager.PERMISSION_GRANTED) {
            return;
        }
        int captureSession = voiceCaptureSession.incrementAndGet();
        releaseAudioRecord();
        AudioRecord recorder = new AudioRecord(MediaRecorder.AudioSource.MIC, AUDIO_SAMPLE_RATE,
                AudioFormat.CHANNEL_IN_MONO, AudioFormat.ENCODING_PCM_16BIT,
                TX_AUDIO_MIN_BUFFER_SIZE);
        if (recorder.getState() != AudioRecord.STATE_INITIALIZED) {
            Log.w(TAG, "AudioRecord initialization failed");
            recorder.release();
            return;
        }
        recorder.startRecording();
        audioRecord.set(recorder);
        voiceCaptureActive = true;
        new Thread(() -> captureVoiceAudio(recorder, captureSession), "Radio voice capture").start();
    }

    private void captureVoiceAudio(AudioRecord recorder, int captureSession) {
        short[] audioBuffer = new short[AUDIO_FRAME_SAMPLES];
        while (isVoiceCaptureSessionActive(recorder, captureSession)) {
            int samples = recorder.read(audioBuffer, 0, AUDIO_FRAME_SAMPLES, AudioRecord.READ_BLOCKING);
            if (samples == AUDIO_FRAME_SAMPLES && isVoiceCaptureSessionActive(recorder, captureSession)) {
                sendAudioToESP32(audioBuffer, false);
            }
        }
    }

    private boolean isVoiceCaptureSessionActive(AudioRecord recorder, int captureSession) {
        return voiceCaptureActive
                && voiceCaptureSession.get() == captureSession
                && audioRecord.get() == recorder;
    }

    private void stopVoiceCapture() {
        if (!voiceCaptureActive && audioRecord.get() == null) {
            return;
        }
        voiceCaptureActive = false;
        voiceCaptureSession.incrementAndGet();
        releaseAudioRecord();
    }

    private void releaseAudioRecord() {
        AudioRecord recorder = audioRecord.getAndSet(null);
        if (recorder == null) {
            return;
        }
        try {
            recorder.stop();
        } catch (IllegalStateException ignored) {
            // Recorder was never started or was already stopped.
        }
        recorder.release();
    }

    public void reconnectViaUSB() {
        Log.i(TAG, connectLog("reconnectViaUSB(): clearing pending state for next attempt"));
        usbPermissionRequestPending = false;
        // Re-plug is an explicit user/device action; allow connection attempts again.
        radioMissingNotified = false;
    }

    public void renegotiateAfterFlashing() {
        Log.i(TAG, connectLog("renegotiateAfterFlashing(): closing port and resetting state before renegotiation"));
        closePortAndReset();
        reconnectViaUSB();
    }

    public void onUsbPermissionDenied() {
        Log.w(TAG, connectLog("USB permission denied by system dialog"));
        usbPermissionRequestPending = false;
        radioMissing();
    }

    private boolean isConnectionReady() {
        return hostToEsp32 != null
            && activeTransport != null
            && activeTransport.isReady();
    }

    private void closePortAndReset() {
        waitingForHello = false;
        cancelHelloTimeout();
        abandonAudioFocus();
        radioModule.detachSender();
        hostToEsp32 = null;
        RadioTransport transport = activeTransport;
        activeTransport = null;
        if (transport != null) {
            try {
                transport.close();
            } catch (Exception ignored) {
                // Best-effort cleanup during teardown.
            }
        }
    }

    private void reconcileConnections() {
        handler.post(this::tickPositionBeacon);
        activeUsbConnectAttemptId = ++usbConnectAttemptSeq;
        Log.d(TAG, connectLog("reconcileConnections(): state=" + connectionStateSummary()));
        Optional<UsbDevice> device = usbManager.getDeviceList().values().stream()
            .filter(this::isESP32Device)
            .findFirst();
        if (isConnectionReady()) {
            return;
        }
        if (device.isPresent()) {
            if (activeTransport instanceof BleKissRadioTransport) {
                closePortAndReset();
            }
            setMode(RadioMode.STARTUP);
            clearRadioTypeAndLimits();
            Log.d(TAG, connectLog("reconcileConnections(): found ESP32 USB device"));
            callbacks.hideSnackBar();
            setupSerialConnection();
            return;
        }
        if (activeTransport == null) {
            setMode(RadioMode.STARTUP);
            clearRadioTypeAndLimits();
            notifyRadioMissing();
            Log.d(TAG, connectLog("reconcileConnections(): no USB device; starting BLE discovery"));
            attemptBleConnect();
        }
    }

    private boolean isESP32Device(UsbDevice device) {
        int vendorId = device.getVendorId();
        int productId = device.getProductId();
        Log.d(TAG, String.format("Checking USB device: vendorId=%d, productId=%d, product=\"%s\"",
            vendorId, productId, device.getProductName()));
        for (int i = 0; i < ESP32_VENDOR_IDS.length; i++) {
            if (vendorId == ESP32_VENDOR_IDS[i] && productId == ESP32_PRODUCT_IDS[i]) {
                return true;
            }
        }
        return false;
    }

    /**
     * Sets up the USB serial connection to the ESP32, and starts listening for data.
     * If no ESP32 is found, it will call radioMissing() on the callbacks.
     */
    public void setupSerialConnection() {
        Log.d(TAG, connectLog("setupSerialConnection(): begin"));
        // Find all available drivers from attached devices.
        UsbManager manager = (UsbManager) getSystemService(Context.USB_SERVICE);
        List<UsbSerialDriver> availableDrivers = UsbSerialProber.getDefaultProber().findAllDrivers(manager);
        if (availableDrivers.isEmpty()) {
            Log.d(TAG, connectLog("setupSerialConnection(): no available USB drivers"));
            radioMissing();
            return;
        }
        // Open a connection to the first available driver.
        UsbSerialDriver driver = availableDrivers.get(0);
        if (!manager.hasPermission(driver.getDevice())) {
            if (usbPermissionRequestPending) {
                Log.d(TAG, connectLog("setupSerialConnection(): USB permission request already pending"));
                return;
            }
            Log.i(TAG, connectLog("setupSerialConnection(): requesting USB permission"));
            usbPermissionRequestPending = true;
            PendingIntent permissionIntent = PendingIntent.getBroadcast(
                this,
                0,
                new Intent(ACTION_USB_PERMISSION),
                PendingIntent.FLAG_UPDATE_CURRENT | PendingIntent.FLAG_IMMUTABLE
            );
            manager.requestPermission(driver.getDevice(), permissionIntent);
            return;
        }
        usbPermissionRequestPending = false;
        UsbDeviceConnection connection = manager.openDevice(driver.getDevice());
        if (connection == null) {
            Log.w(TAG, connectLog("setupSerialConnection(): couldn't open USB device"));
            radioMissing();
            return;
        }
        UsbSerialPort serialPort = driver.getPorts().get(0); // Most devices have just one port (port 0)
        Log.d(TAG, connectLog("setupSerialConnection(): serialPort=" + serialPort));
        try {
            serialPort.open(connection);
            serialPort.setParameters(115200, 8, UsbSerialPort.STOPBITS_1, UsbSerialPort.PARITY_NONE);
        } catch (Exception e) {
            Log.w(TAG, connectLog("setupSerialConnection(): couldn't open USB serial port"), e);
            try {
                serialPort.close();
            } catch (Exception ignored) {
                // Best-effort cleanup after a partial open.
            }
            radioMissing();
            return;
        }
        try { // These settings needed for better data transfer on Adafruit QT Py ESP32-S2
            serialPort.setRTS(true);
            serialPort.setDTR(true);
        } catch (Exception e) {
            // Ignore, may not be supported on all devices.
        }
        RadioTransport transport = new UsbSerialRadioTransport(serialPort, handler);
        activeTransport = transport;
        transport.start(createTransportListener(transport));
    }

    private void attemptBleConnect() {
        RadioTransport transport = new BleKissRadioTransport(this, handler);
        activeTransport = transport;
        transport.start(createTransportListener(transport));
    }

    private RadioTransport.Listener createTransportListener(RadioTransport transport) {
        return new RadioTransport.Listener() {
            @Override
            public void onBytes(byte[] bytes) {
                processRadioBytes(bytes);
            }

            @Override
            public void onReady() {
                if (activeTransport != transport) {
                    return;
                }
                callbacks.hideSnackBar();
                hostToEsp32 = new Protocol.Sender(transport::writeAsync);
                radioModule.attachSender(hostToEsp32);
                Log.i(TAG, connectLog(transport.getName() + " connected; starting handshake"));
                startProtocolHandshake();
            }

            @Override
            public void onDisconnected() {
                if (activeTransport == transport) {
                    Log.i(TAG, connectLog(transport.getName() + " disconnected"));
                    radioMissing();
                }
            }

            @Override
            public void onError(Exception error) {
                if (activeTransport == transport) {
                    Log.w(TAG, connectLog(transport.getName() + " transport error"), error);
                    if (audioTrack != null) {
                        audioTrack.stop();
                    }
                    radioMissing();
                }
            }
        };
    }

    private synchronized void processRadioBytes(byte[] data) {
        esp32DataStreamParser.processBytes(data);
    }

    public void radioConnected() {
        Log.i(TAG, connectLog("radioConnected(): handshake complete; state=" + connectionStateSummary()));
        radioMissingNotified = false;
        // Acquire WakeLock if not already held to ensure audio processing continues in background.
        if (wakeLock != null && !wakeLock.isHeld()) {
            wakeLock.acquire();
        }
        callbacks.radioConnected();
    }

    private void startProtocolHandshake() {
        int handshakeId = ++handshakeSeq;
        activeHandshakeId = handshakeId;
        waitingForHello = true;
        callbacks.radioModuleHandshake();
        Log.i(TAG, handshakeLog(handshakeId, "start(): waiting for HELLO(version)"));
        scheduleHelloTimeout(handshakeId);
    }

    private void scheduleHelloTimeout(int handshakeId) {
        cancelHelloTimeout();
        helloTimeoutRunnable = () -> {
            if (!waitingForHello || activeHandshakeId != handshakeId) {
                return;
            }
            waitingForHello = false;
            Log.w(TAG, handshakeLog(handshakeId, "waitForHello(): timed out after " + HELLO_TIMEOUT_MS + "ms"));
            setMode(RadioMode.BAD_FIRMWARE);
            callbacks.missingFirmware();
        };
        handler.postDelayed(helloTimeoutRunnable, HELLO_TIMEOUT_MS);
    }

    private void cancelHelloTimeout() {
        if (helloTimeoutRunnable != null) {
            handler.removeCallbacks(helloTimeoutRunnable);
            helloTimeoutRunnable = null;
        }
    }

    private void handleHelloReceived(Optional<Protocol.Hello> hello) {
        int handshakeId;
        if (waitingForHello) {
            waitingForHello = false;
            handshakeId = activeHandshakeId;
            cancelHelloTimeout();
            Log.d(TAG, handshakeLog(handshakeId, "HELLO received: " + hello));
        } else {
            handshakeId = ++handshakeSeq;
            activeHandshakeId = handshakeId;
            Log.i(TAG, handshakeLog(handshakeId, "HELLO received outside active wait; validating firmware state"));
        }
        validateHello(handshakeId, hello);
    }

    private void validateHello(int handshakeId, Optional<Protocol.Hello> hello) {
        if (!hello.isPresent()) {
            Log.e(TAG, handshakeLog(handshakeId, "HELLO missing valid Hello payload; firmware upgrade required"));
            callbacks.outdatedFirmware(0);
            setMode(RadioMode.BAD_FIRMWARE);
            return;
        }

        Protocol.Hello helloPayload = hello.get();
        Protocol.FirmwareVersion version = helloPayload.getVersion();
        Log.d(TAG, handshakeLog(handshakeId, "hello=" + helloPayload));
        if (version.getVer() < FirmwareUtils.PACKAGED_FIRMWARE_VER) {
            callbacks.outdatedFirmware(version.getVer());
            setMode(RadioMode.BAD_FIRMWARE);
            return;
        }

        handleHello(helloPayload);
        if (Protocol.RadioStatus.RADIO_STATUS_NOT_FOUND.equals(version.getRadioModuleStatus())) {
            Log.w(TAG, handshakeLog(handshakeId, "radio module not found"));
            setMode(RadioMode.BAD_FIRMWARE);
            callbacks.radioModuleNotFound();
            return;
        }

        getHostToEsp32().setFlowControlWindow(version.getWindowSize());
        handleInitialDeviceState(helloPayload.getDeviceState());
        markRadioTransportReady();
        Log.i(TAG, handshakeLog(handshakeId, "HELLO version OK; proceeding with radio communication"));
        setMode(RadioMode.RX);
        openFirmwareAudio();
        // Turn off scanning if it was on (e.g. if radio was unplugged briefly and reconnected)
        setScanning(false);
        radioConnected();
    }

    private String handshakeLog(int handshakeId, String message) {
        return "handshake#" + handshakeId
            + "/connect#" + getActiveUsbConnectAttemptId()
            + " " + threadTag()
            + " " + message;
    }

    // Called in many situations where radio connection is found to be broken
    private void radioMissing() {
        Log.i(TAG, connectLog("radioMissing(): state=" + connectionStateSummary()));
        stopVoiceCapture();
        closePortAndReset();
        notifyRadioMissing();
        if (wakeLock != null && wakeLock.isHeld()) {
            wakeLock.release(); // Don't keep screen on
        }
    }

    private void notifyRadioMissing() {
        if (!radioMissingNotified) {
            radioMissingNotified = true;
            callbacks.radioMissing(); // Notify UI only on transition into missing state
        }
    }

    int getActiveUsbConnectAttemptId() {
        return activeUsbConnectAttemptId;
    }

    private String connectLog(String message) {
        return "connect#" + activeUsbConnectAttemptId + " " + threadTag() + " " + message;
    }

    private String connectionStateSummary() {
        return "mode=" + mode
            + ",hostToEsp32=" + (hostToEsp32 != null)
            + ",activeTransport=" + (activeTransport != null ? activeTransport.getName() : "null")
            + ",activeTransportReady=" + (activeTransport != null && activeTransport.isReady())
            + ",usbPermissionPending=" + usbPermissionRequestPending
            + ",radioMissingNotified=" + radioMissingNotified;
    }

    static String threadTag() {
        Thread thread = Thread.currentThread();
        return "thread=" + thread.getName() + "#" + thread.getId();
    }

    public RadioModuleType getRadioType() {
        Protocol.RfModuleType rfModuleType = radioModule.getRfModuleType();
        if (Protocol.RfModuleType.RF_SA818_UHF.equals(rfModuleType)) {
            return RadioModuleType.UHF;
        }
        if (Protocol.RfModuleType.RF_SA818_VHF.equals(rfModuleType)) {
            return RadioModuleType.VHF;
        }
        return RadioModuleType.UNKNOWN;
    }

    private void clearRadioTypeAndLimits() {
        radioModule.clearFirmwareVersion();
        callbacks.setRadioType(RadioModuleType.UNKNOWN);
    }

    public void handleHello(Protocol.Hello hello) {
        radioModule.seedFirmwareVersion(hello.getVersion());
        callbacks.setRadioType(getRadioType());
        updateTxLimitsForBand();
    }

    public void updateTxLimitsForBand() {
        if (RadioModuleType.VHF.equals(getRadioType())) {
            setMinTxFreq(min2mTxFreq);
            setMaxTxFreq(max2mTxFreq);
        } else if (RadioModuleType.UHF.equals(getRadioType())) {
            setMinTxFreq(min70cmTxFreq);
            setMaxTxFreq(max70cmTxFreq);
        }
        Log.d(TAG, "Radio type set to: " + getRadioType());
        Log.d(TAG, "Min radio freq: " + getMinRadioFreq());
        Log.d(TAG, "Max radio freq: " + getMaxRadioFreq());
        Log.d(TAG, "Min tx freq: " + minTxFreq);
        Log.d(TAG, "Max tx freq: " + maxTxFreq);
        float txFrequency = radioModule.getTxFrequency() > 0 ? radioModule.getTxFrequency() : parseActiveFrequencyOrZero();
        updateTxAllowed(txFrequency);
        Log.d(TAG, String.format("Tx allowed: %b (%s)", isTxAllowed(), txFrequency));
    }

    private float parseActiveFrequencyOrZero() {
        if (activeFrequencyStr == null) {
            return 0.0f;
        }
        try {
            return Float.parseFloat(activeFrequencyStr);
        } catch (NumberFormatException e) {
            return 0.0f;
        }
    }

    private Long activeFrequencyHz() {
        try {
            return Math.round(Double.parseDouble(activeFrequencyStr) * 1_000_000d);
        } catch (NumberFormatException e) {
            return null;
        }
    }

    private Long activeTxFrequencyHz() {
        return AprsRfFrequencyPolicy.toHz(radioModule.getDesiredTxFrequency());
    }

    public boolean isHasHighLowPowerSwitch() {
        return radioModule.hasHighLowPowerSwitch();
    }

    public boolean isHasPhysPttButton() {
        return radioModule.hasPhysPttButton();
    }

    public boolean supportsFreeDv2400b() {
        return radioModule.supportsFreeDv2400b();
    }

    public synchronized boolean isFreeDv2400bEnabled() {
        return freeDv2400bEnabled;
    }

    public synchronized void setFreeDv2400bEnabled(boolean enabled) {
        enabled = enabled && supportsFreeDv2400b();
        if (enabled && codec2 == null) codec2 = new Codec2();
        freeDv2400bEnabled = enabled;
        codec2TxSamples = 0;
        codec2HasPendingInput = false;
        radioModule.setFreeDv2400b(enabled);
    }

    public float getMinRadioFreq() {
        return radioModule.getMinRadioFreq();
    }

    public float getMaxRadioFreq() {
        return radioModule.getMaxRadioFreq();
    }

    public void setScanning(boolean scanning, boolean goToRxMode) {
        if (!scanning && mode != RadioMode.SCAN) {
            return;
        }
        if (!scanning) {
            cancelPendingScanAdvance();
            if (scanBaseSquelch >= 0 && scanBaseSquelch != radioModule.getDesiredSquelch()) {
                radioModule.beginUpdate();
                try {
                    radioModule.setSquelch((byte) scanBaseSquelch);
                    if (activeMemoryId > -1) {
                        tuneToMemory(activeMemoryId);
                    } else {
                        tuneToFreq(activeFrequencyStr);
                    }
                } finally {
                    radioModule.endUpdate();
                }
            }
            scanBaseSquelch = -1;
            if (goToRxMode) {
                setMode(RadioMode.RX);
            }
        } else { // Start scanning
            scanBaseSquelch = radioModule.getDesiredSquelch();
            setMode(RadioMode.SCAN);
            nextScan();
        }
    }

    public void setScanning(boolean scanning) {
        setScanning(scanning, true);
    }

    public void nextScan() {
        cancelPendingScanAdvance();
        // Only proceed if actually in SCAN mode.
        if (getMode() != RadioMode.SCAN) {
            return;
        }
        // Make sure channelMemoriesLiveData is set and has items.
        if (channelMemoriesLiveData == null) {
            Log.d(TAG, "Error: attempted nextScan() but channelMemories was never set.");
            return;
        }
        List<ChannelMemory> channelMemories = channelMemoriesLiveData.getValue();
        if (channelMemories == null || channelMemories.isEmpty()) {
            return;
        }
        int currentIndex = indexOfActiveMemory(channelMemories);
        // If we’re in simplex (activeMemoryId == -1), treat it as if
        // the "current index" is -1 so the next index starts at 0.
        int nextIndex = (currentIndex + 1) % channelMemories.size();
        int firstTriedIndex = nextIndex;  // So we know when we've looped around.
        do {
            ChannelMemory candidate = channelMemories.get(nextIndex);
            // If not marked as skipped, and it's in the active band, we tune to it and return.
            if (scanToMemoryIfEligible(candidate)) {
                return;
            }
            // Otherwise, move on to the next memory in the list.
            nextIndex = (nextIndex + 1) % channelMemories.size();
            // Repeat until we loop back to the first tried index.
        } while (nextIndex != firstTriedIndex);
        // If we reach here, all memories are marked skipDuringScan.
        Log.d(TAG, "Warning: All memories are skipDuringScan, no next memory found to scan to.");
    }

    private int indexOfActiveMemory(List<ChannelMemory> channelMemories) {
        for (int i = 0; i < channelMemories.size(); i++) {
            if (channelMemories.get(i).memoryId == activeMemoryId) {
                return i;
            }
        }
        return -1;
    }

    private boolean scanToMemoryIfEligible(ChannelMemory candidate) {
        float frequency;
        try {
            frequency = Float.parseFloat(candidate.frequency);
        } catch (NumberFormatException e) {
            Log.d(TAG, "Memory with id " + candidate.memoryId + " had invalid frequency.");
            return false;
        }
        if (candidate.skipDuringScan || frequency < getMinRadioFreq() || frequency > getMaxRadioFreq()) {
            return false;
        }
        int desiredSquelch = scanBaseSquelch >= 0 ? scanBaseSquelch : radioModule.getDesiredSquelch();
        radioModule.beginUpdate();
        try {
            radioModule.setSquelch((byte) (desiredSquelch > 0 ? desiredSquelch : DEFAULT_SCAN_SQUELCH));
            tuneToMemory(candidate);
        } finally {
            radioModule.endUpdate();
        }
        callbacks.scannedToMemory(candidate.memoryId);
        return true;
    }

    private short[] applyMicGain(short[] audioBuffer, int samples) {
        if (micGainBoost == MicGainBoost.NONE) {
            return audioBuffer; // No gain, just return original
        }
        float gain = micGainBoost.getGain();
        for (int i = 0; i < samples; i++) {
            int sample = Math.round(audioBuffer[i] * gain);
            if (sample > Short.MAX_VALUE) {
                sample = Short.MAX_VALUE;
            } else if (sample < Short.MIN_VALUE) {
                sample = Short.MIN_VALUE;
            }
            audioBuffer[i] = (short) sample;
        }
        return audioBuffer;
    }

    public void sendAudioToESP32(short[] samples, boolean dataMode) {
        Protocol.Sender sender = hostToEsp32;
        if (sender == null) {
            return; // If connection is lost, just drop the audio frame.
        }
        if (freeDv2400bEnabled && !dataMode) {
            sendFreeDvAudio(sender, samples);
            return;
        }
        if (!dataMode) {
            applyMicGain(samples, AUDIO_FRAME_SAMPLES);
        }
        int encodedLength = txAudioEncoder.encodeBlock(samples, 0, AUDIO_FRAME_SAMPLES, txAudioFrame, 0);
        sender.txAudio(txAudioFrame, encodedLength);
    }

    private synchronized void sendFreeDvAudio(Protocol.Sender sender, short[] samples) {
        if (codec2 == null) return;
        applyMicGain(samples, samples.length);
        // The app captures at 16 kHz; Codec2 1300 consumes 320 samples at 8 kHz.
        for (short sample : samples) {
            if (!codec2HasPendingInput) {
                codec2PendingInput = sample;
                codec2HasPendingInput = true;
                continue;
            }
            codec2TxPcm[codec2TxSamples++] = (short) ((codec2PendingInput + sample) / 2);
            codec2HasPendingInput = false;
            if (codec2TxSamples == Codec2.PCM_SAMPLES) {
                codec2.encode(codec2TxPcm, codec2Frame);
                sender.txDigital(codec2Frame);
                codec2TxSamples = 0;
            }
        }
    }

    public boolean isRadioConnected() {
        return isConnectionReady() && mode != RadioMode.STARTUP;
    }

    public boolean canFlashFirmware() {
        return activeTransport != null
            && activeTransport.isReady()
            && activeTransport.supportsFirmwareFlashing();
    }

    public UsbSerialPort getSerialPort() {
        if (activeTransport instanceof UsbSerialRadioTransport) {
            return ((UsbSerialRadioTransport) activeTransport).getSerialPort();
        }
        return null;
    }

    /**
     * Handles the parsed command received from the ESP32.
     * It processes various commands such as S-meter reports, PTT control,
     * debug messages, HELLO command, RX audio, version information, and window updates.
     *
     * @param cmd   The command received from the ESP32.
     * @param param The parameters associated with the command.
     * @param len   The length of the parameters.
     */
    @SuppressWarnings({"java:S6541"})
    private void handleParsedCommand(final RcvCommand cmd, final ByteBuffer param, final int offset, final int len) {
        switch (cmd) {
            case COMMAND_DEBUG_INFO:
                Log.i(FIRMWARE_TAG, firmwareString(param, offset, len));
                break;

            case COMMAND_DEBUG_DEBUG:
                Log.d(FIRMWARE_TAG, firmwareString(param, offset, len));
                break;

            case COMMAND_DEBUG_ERROR:
                Log.e(FIRMWARE_TAG, firmwareString(param, offset, len));
                break;

            case COMMAND_DEBUG_WARN:
                Log.w(FIRMWARE_TAG, firmwareString(param, offset, len));
                break;

            case COMMAND_DEBUG_TRACE:
                Log.v(FIRMWARE_TAG, firmwareString(param, offset, len));
                break;

            case COMMAND_HELLO:
                handleHelloReceived(Protocol.Hello.from(param, offset, len));
                break;

            case COMMAND_RX_AUDIO:
                handleRxAudio(param, offset, len);
                break;

            case COMMAND_RX_DIGITAL:
                handleRxDigital(param, offset, len);
                break;

            case COMMAND_WINDOW_UPDATE:
                WindowUpdate.from(param, offset, len).ifPresent(windowAck ->
                    hostToEsp32.enlargeFlowControlWindow(windowAck.getSize()));
                break;

            case COMMAND_DEVICE_STATE:
                Protocol.DeviceState.from(param, offset, len).ifPresent(this::handleDeviceState);
                break;

            default:
                break;
        }
    }

    private String firmwareString(ByteBuffer param, int offset, int len) {
        if (param == null || !param.hasArray() || offset < 0 || len <= 0 || param.limit() < offset + len) {
            return "";
        }
        return new String(param.array(), offset, len, StandardCharsets.UTF_8);
    }

    private void handleEsp32Ax25Packet(final ByteBuffer param, final int offset, final int len) {
        if (param == null || !param.hasArray() || len < 1 || offset < 0 || param.limit() < offset + len) {
            return;
        }
        handleAx25Packet(param.array(), offset, len);
    }

    void handleInitialDeviceState(Protocol.DeviceState state) {
        radioModule.seedFromDeviceState(state);
        freeDv2400bEnabled = radioModule.isFreeDv2400bEnabled();
        if (state.hasRadioConfig()) {
            activeFrequencyStr = formatFreq(state.getFreqRx());
            activeMemoryId = state.getMemoryId();
        }
        handleDeviceState(state);
        updateNotificationFromCurrentState();
        callbacks.initialDeviceStateReceived();
    }

    void markRadioTransportReady() {
        radioModule.markTransportReady();
    }

    private void handleDeviceState(Protocol.DeviceState state) {
        radioModule.updateDeviceState(state);
        syncFreeDvModeFromDevice();
        syncActiveRadioConfig(state);
        final boolean deviceTxActive = radioModule.isDeviceTxActive();
        final boolean squelched = radioModule.isSquelched();
        callbacks.moduleStateChanged(deviceTxActive, squelched);
        updateAudioFocusForSquelch(squelched);
        if (radioModule.isAppliedStateInSync() && radioModule.getTxFrequency() > 0) {
            updateTxAllowed(radioModule.getTxFrequency());
        }
        if (deviceTxActive || getMode() == RadioMode.RX || getMode() == RadioMode.SCAN) {
            callbacks.sMeterUpdate(radioModule.getSMeterBarValue());
        }
        checkScanDueToSquelch();
        if (radioModule.didPhysPttChange()) {
            boolean physPttDown = radioModule.isPhysPttDown();
            if (physPttDown) {
                if (getMode() == RadioMode.RX && isTxAllowed()) {
                    startPtt();
                    callbacks.forcedPttStart();
                }
            } else if (getMode() == RadioMode.TX) {
                endPtt();
                callbacks.forcedPttEnd();
            }
        }
    }

    private void syncFreeDvModeFromDevice() {
        boolean enabled = radioModule.isFreeDv2400bEnabled();
        if (enabled && codec2 == null) codec2 = new Codec2();
        if (freeDv2400bEnabled == enabled) return;

        freeDv2400bEnabled = enabled;
        codec2TxSamples = 0;
        codec2HasPendingInput = false;
        callbacks.freeDvModeChanged(enabled);
    }

    private void syncActiveRadioConfig(Protocol.DeviceState state) {
        if (!state.hasRadioConfig() || state.getLastError() != 0) {
            return;
        }
        if (!radioModule.isAppliedStateInSync()) {
            return;
        }
        String nextFrequency = formatFreq(state.getFreqRx());
        int nextMemoryId = state.getMemoryId();
        if (nextMemoryId == activeMemoryId && nextFrequency.equals(activeFrequencyStr)) {
            return;
        }
        activeFrequencyStr = nextFrequency;
        activeMemoryId = nextMemoryId;
        updateNotificationFromCurrentState();
        callbacks.radioConfigChanged();
    }

    /**
     * Handles incoming audio data from the ESP32, decoding it and playing it through the AudioTrack.
     * If in RX or SCAN mode, it processes the audio samples and manages the AFSK demodulator.
     * In SCAN mode, firmware squelch state determines whether scanning should advance.
     *
     * @param param The byte array containing the audio data.
     * @param len   The length of the audio data in bytes.
     */
    private void handleRxAudio(final ByteBuffer param, final int offset, final int len) {
        if (param == null || !param.hasArray() || offset < 0 || len <= 0 || param.limit() < offset + len) {
            return;
        }
        int decoded = ImaAdpcm.decodeBlock(param.array(), offset, len, pcm16, 0, AUDIO_FRAME_SAMPLES);

        if ((getMode() == RadioMode.RX || getMode() == RadioMode.SCAN) && audioTrack != null) {
            audioTrack.write(pcm16, 0, decoded, AudioTrack.WRITE_NON_BLOCKING);
            ensureAudioPlaying();
        }
    }

    private synchronized void handleRxDigital(final ByteBuffer param, final int offset, final int len) {
        if (!freeDv2400bEnabled || codec2 == null || param == null || !param.hasArray()
            || len != Codec2.FRAME_BYTES || offset < 0 || param.limit() < offset + len) return;
        System.arraycopy(param.array(), offset, codec2Frame, 0, Codec2.FRAME_BYTES);
        decodeAndPlayFreeDvFrame(codec2Frame);
    }

    private void decodeAndPlayFreeDvFrame(byte[] frame) {
        if (codec2 == null || frame == null || frame.length < Codec2.FRAME_BYTES) return;
        codec2.decode(frame, codec2RxPcm);
        for (int i = 0; i < Codec2.PCM_SAMPLES; i++) {
            codec2PlaybackPcm[i * 2] = codec2RxPcm[i];
            codec2PlaybackPcm[i * 2 + 1] = codec2RxPcm[i];
        }
        if ((getMode() == RadioMode.RX || getMode() == RadioMode.SCAN) && audioTrack != null) {
            audioTrack.write(codec2PlaybackPcm, 0, codec2PlaybackPcm.length, AudioTrack.WRITE_NON_BLOCKING);
            requestAudioFocus();
            ensureAudioPlaying();
        }
    }

    private void updateAudioFocusForSquelch(boolean squelched) {
        if (!squelched && (getMode() == RadioMode.RX || getMode() == RadioMode.SCAN)) {
            requestAudioFocus();
        } else {
            abandonAudioFocus();
        }
    }

    private void requestAudioFocus() {
        if (hasAudioFocus || audioFocusRequest == null) {
            return;
        }
        AudioManager audioManager = (AudioManager) getSystemService(Context.AUDIO_SERVICE);
        hasAudioFocus = audioManager.requestAudioFocus(audioFocusRequest)
            == AudioManager.AUDIOFOCUS_REQUEST_GRANTED;
    }

    private void abandonAudioFocus() {
        if (!hasAudioFocus || audioFocusRequest == null) {
            return;
        }
        AudioManager audioManager = (AudioManager) getSystemService(Context.AUDIO_SERVICE);
        audioManager.abandonAudioFocusRequest(audioFocusRequest);
        hasAudioFocus = false;
    }

    /**
     * Ensures that the AudioTrack is playing and gradually adjusts its volume.
     * The volume is increased smoothly based on a factor of alpha.
     * This method is intended to apply smooth volume adjustments to the AudioTrack.
     * <p>
     * The method first checks if the AudioTrack is playing. If it is not playing, the method starts the playback.
     * Then, the volume is adjusted by applying a smoothing factor using a simple exponential-like formula.
     * </p>
     *
     * @see AudioTrack
     * @see AudioTrack#setVolume(float)
     */
    private void ensureAudioPlaying() {
        if (audioTrack.getPlayState() != AudioTrack.PLAYSTATE_PLAYING) {
            audioTrackVolume = 0;
            audioTrack.setVolume(0.0f);
            audioTrack.play();
        }
        float alpha = 0.02f;
        audioTrackVolume = alpha + (1.0f - alpha) * audioTrackVolume;
        if (audioTrackVolume > 0.7f) {
            audioTrack.setVolume(audioTrackVolume);
        }
        else {
            audioTrack.setVolume(0.0f);
        }
    }

    private void handleAx25Packet(byte[] packet, int offset, int len) {
        try {
            byte[] rawAx25 = java.util.Arrays.copyOfRange(packet, offset, offset + len);
            APRSPacket aprsPacket = Parser.parseAX25(packet, offset, len);

            APRSPacket queuedPacket = aprsPacket.copy();
            byte[] queuedFrame = rawAx25.clone();
            Long frequencyHz = activeFrequencyHz();
            executeAprs(() -> aprsController.handle(queuedPacket, AprsSource.RX_RF,
                frequencyHz, queuedFrame));
        } catch (Exception e) {
            Log.d(TAG, "Unable to parse an APRS packet, skipping.");
        }
    }

    /**
     * Sends a position beacon via APRS.
     * Beaconing is blocked while scanning, including dedicated-frequency beacons.
     * If Google Play Services are not available, it will call unknownLocation() on the callbacks.
     */
    @RequiresPermission(allOf = {Manifest.permission.ACCESS_FINE_LOCATION, Manifest.permission.ACCESS_COARSE_LOCATION})
    public void sendPositionBeacon() {
        // Beaconing while scanning is intentionally skipped.
        // The firmware can temporarily override frequency for AX.25 TX, but scan
        // updates may change desired radio state while the override is waiting for
        // channel access. Keep scan/beacon interaction simple for now.
        if (getMode() == RadioMode.SCAN) {
            Log.d(TAG, "Skipping position beacon: scanning is active.");
            return;
        }
        if (!isRadioConnected() || !isTxAllowed()) {
            Log.d(TAG, "Skipping position beacon: radio disconnected or tx not allowed.");
            return;
        }

        if (!AprsRfFrequencyPolicy.allowsMode(getMode())) {
            Log.d(TAG, "Skipping position beacon: mode does not allow this beacon frequency.");
            return;
        }

        if (GoogleApiAvailability.getInstance().isGooglePlayServicesAvailable(getBaseContext()) != ConnectionResult.SUCCESS) {
            Log.d(TAG, "Can't get GPS position: missing Google Play Services.");
            callbacks.unknownLocation();
            return;
        }
        FusedLocationProviderClient locationClient = LocationServices.getFusedLocationProviderClient(this);
        CancellationToken token = new CancellationTokenSource().getToken();
        locationClient.getCurrentLocation(Priority.PRIORITY_HIGH_ACCURACY, token)
            .addOnSuccessListener(location -> {
                if (location != null) {
                    updateAprsIsFilterLocation(location.getLatitude(), location.getLongitude());
                    performPositionBeacon(location.getLatitude(), location.getLongitude());
                } else {
                    callbacks.unknownLocation();
                }
            }).addOnFailureListener(e -> callbacks.unknownLocation());
    }

    private void performPositionBeacon(final double latitude, final double longitude) {
        if (CURRENT_FREQUENCY.equals(aprsBeaconFrequency)) {
            callbacks.startingAprsBeacon(activeFrequencyStr);
            sendPositionBeaconOnActiveChannel(latitude, longitude, activeFrequencyStr);
            return;
        }

        final float beaconFrequency;
        try {
            beaconFrequency = Float.parseFloat(makeSafeHamFreq(aprsBeaconFrequency));
        } catch (NumberFormatException e) {
            Log.w(TAG, "Skipping position beacon: invalid beacon frequency " + aprsBeaconFrequency, e);
            return;
        }
        if (!canTransmitOnFrequency(beaconFrequency) || !isTxAllowed()) {
            Log.d(TAG, "Skipping position beacon: beacon frequency is not permitted for TX.");
            return;
        }

        callbacks.startingAprsBeacon(aprsBeaconFrequency);
        sendPositionBeaconOnSideChannel(latitude, longitude, beaconFrequency, aprsBeaconFrequency);
    }

    private void sendPositionBeaconOnActiveChannel(final double latitude, final double longitude,
                                                   final String beaconFrequency) {
        sendPositionBeacon(latitude, longitude, null, beaconFrequency);
    }

    private void sendPositionBeaconOnSideChannel(final double latitude, final double longitude,
                                                 final float txFrequency, final String beaconFrequency) {
        sendPositionBeacon(latitude, longitude, txFrequency, beaconFrequency);
    }

    /**
     * Sends a position beacon via APRS.
     * Beaconing is blocked while scanning, including dedicated-frequency beacons.
     *
     * @param latitude  The latitude to beacon.
     * @param longitude The longitude to beacon.
     * @param txFrequency Frequency for a temporary TX override, or null for the active channel.
     * @param beaconFrequency Display frequency for this beacon.
     */
    private void sendPositionBeacon(final double latitude, final double longitude, final Float txFrequency,
                                    final String beaconFrequency) {
        if (!AprsRfFrequencyPolicy.allowsMode(getMode())) {
            Log.d(TAG, "Skipping position beacon because mode does not allow this beacon frequency");
            return;
        }
        final boolean isApprox = aprsPositionAccuracy == APRS_POSITION_APPROX;
        final double beaconLatitude = isApprox ? Math.round(latitude * 100.0) / 100.0 : latitude;
        final double beaconLongitude = isApprox ? Math.round(longitude * 100.0) / 100.0 : longitude;
        final BeaconData beacon = BeaconData.builder()
            .latitude(beaconLatitude).longitude(beaconLongitude)
            .symbolTable('/').symbolCode(aprsPositionIcon.getCode())
            .messagingCapable(true).compressed(true).build();
        executeAprs(() -> {
            boolean accepted = false;
            try {
                aprsBeaconTxOverrideMhz = txFrequency;
                accepted = aprsController.submitPositionBeacon(beacon);
                if (!accepted) Log.d(TAG, "Position beacon was not accepted");
            } catch (RuntimeException e) {
                // A persistence failure after RF submission must not trigger an automatic resend.
                Log.w(TAG, "Unable to submit or record APRS position beacon", e);
            } finally {
                aprsBeaconTxOverrideMhz = null;
            }
            final boolean sent = accepted;
            handler.post(() -> {
                if (sent) callbacks.sentAprsBeacon(beaconLatitude, beaconLongitude, beaconFrequency, false);
            });
        });
    }

    /**
     * Sends a chat message to the specified recipient.
     *
     * @param to   The callsign of the recipient, or null for BLN1CQ.
     * @param text The message text to send.
     */
    public void sendChatMessage(String to, String text) {
        // Sanitize message text
        final String outText = text.replace('|', ' ').replace('~', ' ').replace('{', ' ');
        final String targetCallsign = (to == null || to.trim().isEmpty()) ? "BLN1CQ" : to;
        if (callsign.trim().isEmpty()) {
            Log.d(TAG, "Error: Tried to send message with no sender callsign.");
            return;
        }
        final Long frequencyHz = activeTxFrequencyHz();
        executeAprs(() -> {
            try {
                if (!aprsController.postMessage(targetCallsign, outText, frequencyHz)) {
                    Log.d(TAG, "Outgoing APRS message was not accepted");
                    handler.post(() -> callbacks.chatError(getString(R.string.aprs_message_not_accepted)));
                }
            } catch (RuntimeException e) {
                // Do not resend after a persistence failure: the frame may already be submitted.
                Log.e(TAG, "Unable to submit or record outgoing APRS message", e);
                handler.post(() -> callbacks.chatError(e.getMessage()));
            }
        });
    }

    // Radio transport and TX safety belong to the service, not its APRS callback adapter.
    @SuppressWarnings("java:S3398")
    private boolean txAX25PacketOnFrequency(Packet ax25Packet, float txFrequency) {
        if (!isTxAllowed() || !canTransmitOnFrequency(txFrequency)) {
            Log.e(TAG, "Tried to send an AX.25 packet on a disallowed frequency, did not send.");
            return false;
        }
        if (!AprsRfFrequencyPolicy.allowsMode(getMode())) {
            Log.e(TAG, "Tried to send an AX.25 packet in an unsupported mode, did not send.");
            return false;
        }
        Protocol.Sender sender = hostToEsp32;
        if (sender == null) {
            Log.e(TAG, "Tried to send AX.25 packet with no ESP32 connection.");
            return false;
        }
        sender.txAx25OnFrequency(txFrequency, radioModule.getDesiredBandwidth(), radioModule.getDesiredTxTone(),
            ax25Packet.bytesWithoutCRC());
        Log.i(TAG, "Send AX25 packet on " + txFrequency + " MHz: " + ax25Packet);
        return true;
    }

    public int getAudioTrackSessionId() {
        return Optional.ofNullable(audioTrack).map(AudioTrack::getAudioSessionId).orElse(-1);
    }

    /**
     * Sets whether radio module should poll RSSI. We need to be able to turn this off
     * because in v1.x versions of the PCB there's cross-talk between the Serial2 trace and
     * the audio trace, which breaks APRS decoding (and any other digital mode we might add).
     * See <a href="https://github.com/VanceVagell/kv4p-ht/issues/310">...</a> for context.
     * <p>
     * This will send the new state to the ESP32 if it is connected.
     *
     * @param on true to enable RSSI, false to disable it.
     */
    public void setRssi(boolean on) {
        radioModule.setRssi(on);
    }

    public boolean isRssiOn() {
        return radioModule.isRssiEnabled();
    }

}
