VanceVagell/kv4p-ht/pcb/v2.1-metal-case/esp32-test-code/kv4p-ht-v2-esp32-test/include/kv4p-ht-v2.h

/*
 * Defines for all the pins, where hardware is attached.
 */

#define PIN_BUTTON_PROGRAM (0)
#define PIN_TX_TO_USB (1)
#define PIN_STOCK_LED (2)
#define PIN_RX_FROM_USB (3)
#define PIN_RADIO_SQUELCH (4)
#define PIN_BUTTON_PTT_RIGHT (5)
#define PIN_GPIOHEAD_2 (12)
#define PIN_NEOPIXEL (13)
#define PIN_GPIOHEAD_4 (14)
#define PIN_GPIOHEAD_6 (15)
#define PIN_RX_FROM_RADIO (16)
#define PIN_TX_TO_RADIO (17)
#define PIN_RADIO_PTT (18)
#define PIN_RADIO_PD (19)
#define PIN_SAOHEAD_SDA (21)
#define PIN_SAOHEAD_SCK (22)
#define PIN_RADIO_HI_LOW (23)
#define PIN_AUDIO_TX_TO_RADIO (25)
#define PIN_SAOHEAD_5 (26)
#define PIN_SAOHEAD_6 (27)
#define PIN_GPIOHEAD_7 (32)
#define PIN_BUTTON_PTT_LEFT (33)
#define PIN_AUDIO_RX_FROM_RADIO (34)
#define PIN_GPIOHEAD_8 (35)
