VanceVagell/kv4p-ht/android-src/KV4PHT/app/src/main/java/com/vagell/kv4pht/ui/SettingsActivity.java

/*
kv4p HT (see http://kv4p.com)
Copyright (C) 2024 Vance Vagell

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
You should have received a copy of the GNU General Public License
along with this program.  If not, see <http://www.gnu.org/licenses/>.
*/

package com.vagell.kv4pht.ui;

import android.app.Activity;
import android.Manifest;
import android.content.ActivityNotFoundException;
import android.content.ComponentName;
import android.content.Context;
import android.content.Intent;
import android.content.pm.PackageManager;
import android.content.ServiceConnection;
import android.content.res.Resources;
import android.graphics.Color;
import android.os.Bundle;
import android.os.IBinder;
import android.text.Editable;
import android.text.TextWatcher;
import android.util.Log;
import android.view.View;
import android.view.WindowManager;
import android.widget.*;

import androidx.appcompat.app.AppCompatActivity;

import androidx.lifecycle.ViewModelProvider;
import com.google.android.material.slider.Slider;

import static com.google.android.material.snackbar.Snackbar.LENGTH_LONG;
import com.google.android.material.snackbar.Snackbar;
import com.google.android.material.textfield.TextInputEditText;
import com.vagell.kv4pht.BuildConfig;
import com.vagell.kv4pht.R;
import com.vagell.kv4pht.data.AprsFeedPolicy;
import com.vagell.kv4pht.data.AppSetting;
import com.vagell.kv4pht.radio.RadioAudioService;

import java.util.Arrays;
import java.util.List;
import java.util.Map;
import java.util.concurrent.ExecutorService;
import java.util.concurrent.Executors;
import java.util.function.Consumer;
import java.util.stream.Collectors;

public class SettingsActivity extends AppCompatActivity {
    private static final String TAG = SettingsActivity.class.getSimpleName();
    private static final int[] APRS_ICON_CHOICE_RESOURCES = {
            R.string.aprs_icon_phone, R.string.aprs_icon_person, R.string.aprs_icon_house,
            R.string.aprs_icon_bicycle, R.string.aprs_icon_car, R.string.aprs_icon_jeep,
            R.string.aprs_icon_truck, R.string.aprs_icon_motorcycle, R.string.aprs_icon_van,
            R.string.aprs_icon_rv, R.string.aprs_icon_18_wheeler, R.string.aprs_icon_glider,
            R.string.aprs_icon_small_aircraft, R.string.aprs_icon_helicopter,
            R.string.aprs_icon_sailboat, R.string.aprs_icon_motorboat
    };
    private static final APRSIconType[] APRS_ICON_TYPES = {
            APRSIconType.T_PHONE, APRSIconType.T_PERSON, APRSIconType.T_HOUSE,
            APRSIconType.T_BICYCLE, APRSIconType.T_CAR, APRSIconType.T_JEEP,
            APRSIconType.T_TRUCK, APRSIconType.T_MOTORCYCLE, APRSIconType.T_VAN,
            APRSIconType.T_RV, APRSIconType.T_18_WHEELER, APRSIconType.T_GLIDER,
            APRSIconType.T_SMALL_AIRCRAFT, APRSIconType.T_HELICOPTER,
            APRSIconType.T_SAILBOAT, APRSIconType.T_MOTORBOAT
    };
    private final ExecutorService threadPoolExecutor = Executors.newSingleThreadExecutor();
    private MainViewModel viewModel = null;
    private boolean hasHighLowPowerSwitch = false;
    private int firmwareVersion = -1;
    public static final String EXTRA_RF_POWER_HIGH = "rfPowerHigh";
    public static final String EXTRA_FREEDV_2400B_ENABLED = "freeDv2400bEnabled";
    public static final String EXTRA_BANDWIDTH = "bandwidth";
    public static final String EXTRA_SQUELCH = "squelch";
    public static final String EXTRA_FILTER_PRE = "filterPre";
    public static final String EXTRA_FILTER_HIGH = "filterHigh";
    public static final String EXTRA_FILTER_LOW = "filterLow";
    public static final String EXTRA_APRS_ICON = "aprsIcon";

    private RadioAudioService radioAudioService = null;
    private boolean radioAudioServiceBound = false;
    private boolean doneClicked = false;

    private int initialSquelch = 0;
    private boolean initialEmphasis = false;
    private boolean initialHighpass = false;
    private boolean initialLowpass = false;

    private final ServiceConnection serviceConnection = new ServiceConnection() {
        @Override
        public void onServiceConnected(ComponentName name, IBinder service) {
            radioAudioService = ((RadioAudioService.RadioBinder) service).getService();
            radioAudioServiceBound = true;
            Log.d(TAG, "RadioAudioService bound for live updates");
        }

        @Override
        public void onServiceDisconnected(ComponentName name) {
            radioAudioService = null;
            radioAudioServiceBound = false;
        }
    };

    @Override
    protected void onCreate(Bundle savedInstanceState) {
        super.onCreate(savedInstanceState);
        viewModel = new ViewModelProvider(this).get(MainViewModel.class);
        hasHighLowPowerSwitch = getIntent().getBooleanExtra("hasHighLowPowerSwitch", false);
        firmwareVersion = getIntent().getIntExtra("firmwareVersion", -1);

        initialSquelch = getIntent().getIntExtra(EXTRA_SQUELCH, 0);
        initialEmphasis = getIntent().getBooleanExtra(EXTRA_FILTER_PRE, false);
        initialHighpass = getIntent().getBooleanExtra(EXTRA_FILTER_HIGH, false);
        initialLowpass = getIntent().getBooleanExtra(EXTRA_FILTER_LOW, false);

        setContentView(R.layout.activity_settings);
        getWindow().addFlags(WindowManager.LayoutParams.FLAG_KEEP_SCREEN_ON);
        populateOriginalValues(() -> {
            attachListeners();
            attachLiveListeners();
        });
        populateBandwidths();
        populateMinFrequencies();
        populateMaxFrequencies();
        populateMicGainOptions();
        populateAprsOptions();
        populateAprsFrequencies();
        populateAprsIcons();
        populateRadioOptions();
        populateVersions();
    }

    @Override
    protected void onStart() {
        super.onStart();
        try {
            Intent intent = new Intent(this, RadioAudioService.class);
            bindService(intent, serviceConnection, Context.BIND_AUTO_CREATE);
        } catch (Exception e) {
            Log.e(TAG, "Error binding to RadioAudioService", e);
        }
    }

    @Override
    protected void onStop() {
        super.onStop();
        if (!doneClicked) {
            revertSettings();
        }
        if (radioAudioServiceBound) {
            unbindService(serviceConnection);
            radioAudioServiceBound = false;
        }
    }

    private void revertSettings() {
        if (radioAudioService != null && radioAudioService.isRadioConnected()) {
            radioAudioService.getRadioModule().beginUpdate();
            try {
                radioAudioService.getRadioModule().setSquelch(initialSquelch);
                radioAudioService.getRadioModule().setFilters(initialEmphasis, initialHighpass, initialLowpass);
            } finally {
                radioAudioService.getRadioModule().endUpdate();
            }
            Log.d(TAG, "Reverted radio settings");
        }
    }

    private void attachLiveListeners() {
        Slider squelchSlider = findViewById(R.id.squelchSlider);
        squelchSlider.addOnChangeListener((slider, value, fromUser) -> {
            if (fromUser && radioAudioService != null && radioAudioService.isRadioConnected()) {
                radioAudioService.getRadioModule().setSquelch((int) value);
            }
        });

        CompoundButton.OnCheckedChangeListener filterListener = (buttonView, isChecked) -> {
            if (radioAudioService != null && radioAudioService.isRadioConnected()) {
                applyFiltersLive();
            }
        };

        ((Switch) findViewById(R.id.emphasisSwitch)).setOnCheckedChangeListener(filterListener);
        ((Switch) findViewById(R.id.highpassSwitch)).setOnCheckedChangeListener(filterListener);
        ((Switch) findViewById(R.id.lowpassSwitch)).setOnCheckedChangeListener(filterListener);
    }

    private void applyFiltersLive() {
        boolean emphasis = ((Switch) findViewById(R.id.emphasisSwitch)).isChecked();
        boolean highpass = ((Switch) findViewById(R.id.highpassSwitch)).isChecked();
        boolean lowpass = ((Switch) findViewById(R.id.lowpassSwitch)).isChecked();
        radioAudioService.getRadioModule().setFilters(emphasis, highpass, lowpass);
    }

    @Override
    protected void onDestroy() {
        super.onDestroy();
        threadPoolExecutor.shutdown();
    }

    private void setDropdownOptions(int viewId, List<String> options) {
        this.<AutoCompleteTextView>findViewById(viewId)
            .setAdapter(new ArrayAdapter<>(this, R.layout.dropdown_item, options));
    }

    private void populateBandwidths() {
        setDropdownOptions(R.id.bandwidthTextView, List.of(getString(R.string.wide), getString(R.string.narrow)));
    }

    private void populateMinFrequencies() {
        setDropdownOptions(R.id.min2mFreqTextView, List.of("144MHz"));
        setDropdownOptions(R.id.min70cmFreqTextView, List.of("420MHz", "430MHz"));
    }

    private void populateMaxFrequencies() {
        setDropdownOptions(R.id.max2mFreqTextView, List.of("148MHz", "146MHz"));
        setDropdownOptions(R.id.max70cmFreqTextView, List.of("450MHz", "440MHz"));
    }

    private void populateMicGainOptions() {
        setDropdownOptions(R.id.micGainBoostTextView, List.of("None", "Low", "Med", "High"));
    }

    private void populateAprsOptions() {
        setDropdownOptions(R.id.aprsPositionAccuracyTextView, List.of("Exact", "Approx"));
        setDropdownOptions(R.id.aprsDestinationFilterTextView, List.of(
            getString(R.string.aprs_show_all), getString(R.string.aprs_only_mine)));
    }

    private void populateAprsFrequencies() {
        setDropdownOptions(R.id.aprsBeaconFreqTextView, List.of(
            getString(R.string.current),
            getString(R.string.freq_144_3900),
            getString(R.string.freq_144_5750),
            getString(R.string.freq_144_6400),
            getString(R.string.freq_144_6600),
            getString(R.string.freq_144_8000),
            getString(R.string.freq_145_1750),
            getString(R.string.freq_145_8250)
        ));
    }

    private void populateAprsIcons() {
        setDropdownOptions(R.id.aprsIconTextView, List.of(
                getString(R.string.aprs_icon_phone),
                getString(R.string.aprs_icon_person),
                getString(R.string.aprs_icon_house),
                getString(R.string.aprs_icon_bicycle),
                getString(R.string.aprs_icon_car),
                getString(R.string.aprs_icon_jeep),
                getString(R.string.aprs_icon_truck),
                getString(R.string.aprs_icon_motorcycle),
                getString(R.string.aprs_icon_van),
                getString(R.string.aprs_icon_rv),
                getString(R.string.aprs_icon_18_wheeler),
                getString(R.string.aprs_icon_glider),
                getString(R.string.aprs_icon_small_aircraft),
                getString(R.string.aprs_icon_helicopter),
                getString(R.string.aprs_icon_sailboat),
                getString(R.string.aprs_icon_motorboat)
        ));
    }

    private void populateRadioOptions() {
        setDropdownOptions(R.id.voiceModeTextView,
            Arrays.asList(getResources().getStringArray(R.array.voice_mode_options)));

        AutoCompleteTextView rfPowerTextView = findViewById(R.id.rfPowerTextView);
        rfPowerTextView.setThreshold(1);
        if (hasHighLowPowerSwitch) {
            rfPowerTextView.setEnabled(true);
            rfPowerTextView.setFocusable(true);
            rfPowerTextView.setClickable(true);
            setDropdownOptions(R.id.rfPowerTextView, Arrays.asList(getResources().getStringArray(R.array.rf_power_options)));
        } else {
            rfPowerTextView.setEnabled(false);
            rfPowerTextView.setFocusable(false);
            rfPowerTextView.setClickable(false);
            rfPowerTextView.setAdapter(null);
            // Set default text to first item
            rfPowerTextView.setText(getResources().getStringArray(R.array.rf_power_options)[0], false);
        }
    }

    private void populateVersions() {
        TextView appVersionTextView = findViewById(R.id.settings_app_version);
        appVersionTextView.setText(appVersionTextView.getText() + " " + BuildConfig.VERSION_NAME);

        TextView firmwareVersionTextView = findViewById(R.id.settings_firmware_version);
        firmwareVersionTextView.setText(firmwareVersionTextView.getText() + " " +
                (firmwareVersion == -1 ? "unknown" : Integer.toString(firmwareVersion)));
    }

    private void setTextIfPresent(Map<String, String> settings, String key, int viewId) {
        if (settings.containsKey(key)) {
            this.<TextInputEditText>findViewById(viewId).setText(settings.get(key));
        }
    }

    private void setSwitchIfPresent(Map<String, String> settings, String key, int viewId) {
        if (settings.containsKey(key)) {
            this.<Switch>findViewById(viewId).setChecked(Boolean.parseBoolean(settings.get(key)));
        }
    }

    private void setDropdownIfPresent(Map<String, String> settings, String key, int viewId) {
        if (settings.containsKey(key)) {
            String dropdownValue = settings.get(key);
            if ("Current".equals(dropdownValue)) {
                dropdownValue = getString(R.string.current);
            }
            this.<AutoCompleteTextView>findViewById(viewId).setText(dropdownValue, false);
        }
    }

    private void setDropdownIfPresent(Map<String, String> settings, String key, int viewId, String suffix) {
        if (settings.containsKey(key)) {
            this.<AutoCompleteTextView>findViewById(viewId)
                .setText(String.format("%s%s", settings.get(key), suffix), false);
        }
    }

    private void populateOriginalValues(Runnable callback) {
        threadPoolExecutor.execute(() -> {
            final Map<String, String> settings = viewModel.getAppDb().appSettingDao().getAll().stream()
                .collect(Collectors.toMap(AppSetting::getName, AppSetting::getValue));
            runOnUiThread(() -> {
                String mhz = getString(R.string.mhz);
                setTextIfPresent(settings, AppSetting.SETTING_CALLSIGN, R.id.callsignTextInputEditText);
                setSwitchIfPresent(settings, AppSetting.SETTING_STICKY_PTT, R.id.stickyPTTSwitch);
                setSwitchIfPresent(settings, AppSetting.SETTING_DISABLE_ANIMATIONS, R.id.noAnimationsSwitch);
                setSwitchIfPresent(settings, AppSetting.SETTING_APRS_BEACON_POSITION, R.id.aprsPositionSwitch);
                if (settings.containsKey(AppSetting.SETTING_APRS_BEACON_FREQUENCY)) {
                    setDropdownIfPresent(settings, AppSetting.SETTING_APRS_BEACON_FREQUENCY, R.id.aprsBeaconFreqTextView);
                } else {
                    this.<AutoCompleteTextView>findViewById(R.id.aprsBeaconFreqTextView).setText(getString(R.string.current), false);
                }
                setDropdownIfPresent(settings, AppSetting.SETTING_APRS_POSITION_ACCURACY, R.id.aprsPositionAccuracyTextView);
                setDropdownIfPresent(settings, AppSetting.SETTING_APRS_ICON, R.id.aprsIconTextView);
                this.<AutoCompleteTextView>findViewById(R.id.aprsDestinationFilterTextView).setText(
                    destinationFilterLabel(
                        settings.get(AppSetting.SETTING_APRS_DESTINATION_FILTER)), false);
                setSwitchIfPresent(settings, AppSetting.SETTING_DIGIPEAT_PACKETS, R.id.digipeatPacketsSwitch);
                setSwitchIfPresent(settings, AppSetting.SETTING_APRS_IGATE, R.id.aprsIgateSwitch);
                setSwitchIfPresent(settings, AppSetting.SETTING_APRS_IS_DISPLAY,
                    R.id.aprsIsDisplaySwitch);
                setRadioSettingsFromIntent();
                setDropdownIfPresent(settings, AppSetting.SETTING_MIN_2_M_TX_FREQ, R.id.min2mFreqTextView, mhz);
                setDropdownIfPresent(settings, AppSetting.SETTING_MAX_2_M_TX_FREQ, R.id.max2mFreqTextView, mhz);
                setDropdownIfPresent(settings, AppSetting.SETTING_MIN_70_CM_TX_FREQ, R.id.min70cmFreqTextView, mhz);
                setDropdownIfPresent(settings, AppSetting.SETTING_MAX_70_CM_TX_FREQ, R.id.max70cmFreqTextView, mhz);
                setDropdownIfPresent(settings, AppSetting.SETTING_MIC_GAIN_BOOST, R.id.micGainBoostTextView);
                callback.run();
            });
        });
    }

    private void setRadioSettingsFromIntent() {
        this.<Slider>findViewById(R.id.squelchSlider).setValue(getIntent().getIntExtra(EXTRA_SQUELCH, 0));
        this.<Switch>findViewById(R.id.emphasisSwitch).setChecked(getIntent().getBooleanExtra(EXTRA_FILTER_PRE, false));
        this.<Switch>findViewById(R.id.highpassSwitch).setChecked(getIntent().getBooleanExtra(EXTRA_FILTER_HIGH, false));
        this.<Switch>findViewById(R.id.lowpassSwitch).setChecked(getIntent().getBooleanExtra(EXTRA_FILTER_LOW, false));
        this.<AutoCompleteTextView>findViewById(R.id.bandwidthTextView)
            .setText(getIntent().getStringExtra(EXTRA_BANDWIDTH) != null ? getIntent().getStringExtra(EXTRA_BANDWIDTH) : getString(R.string.wide), false);

        String[] powerOptions = getResources().getStringArray(R.array.rf_power_options);
        if (powerOptions.length > 0) {
            this.<AutoCompleteTextView>findViewById(R.id.rfPowerTextView)
                .setText(powerOptions[getIntent().getBooleanExtra(EXTRA_RF_POWER_HIGH, true) ? 0 : Math.min(1, powerOptions.length - 1)], false);
        }

        String[] voiceModeOptions = getResources().getStringArray(R.array.voice_mode_options);
        if (voiceModeOptions.length > 0) {
            this.<AutoCompleteTextView>findViewById(R.id.voiceModeTextView)
                .setText(voiceModeOptions[getIntent().getBooleanExtra(EXTRA_FREEDV_2400B_ENABLED, false)
                    ? Math.min(1, voiceModeOptions.length - 1) : 0], false);
        }
    }

    private String destinationFilterLabel(String value) {
        if (value != null && AprsFeedPolicy.DESTINATION_MINE.equalsIgnoreCase(value)) {
            return getString(R.string.aprs_only_mine);
        }
        return getString(R.string.aprs_show_all);
    }

    public void closedCaptionsButtonClicked(View view) { // NOSONAR S1172: XML onClick signature requires View.
        try {
            startActivity(new Intent("com.android.settings.action.live_caption"));
        } catch (ActivityNotFoundException anfe) {
            CharSequence snackbarMsg = "This phone model doesn't support closed captions";
            Snackbar ccSnackbar = Snackbar.make(findViewById(R.id.settingsTopLevelView), snackbarMsg, LENGTH_LONG)
                    .setBackgroundTint(Color.rgb(140, 20, 0)).setActionTextColor(Color.WHITE).setTextColor(Color.WHITE);

            // Make the text of the snackbar larger.
            TextView snackbarActionTextView = (TextView) ccSnackbar.getView().findViewById(com.google.android.material.R.id.snackbar_action);
            snackbarActionTextView.setTextSize(20);
            TextView snackbarTextView = ccSnackbar.getView().findViewById(com.google.android.material.R.id.snackbar_text);
            snackbarTextView.setTextSize(20);

            ccSnackbar.show();
        }
    }

    public void doneButtonClicked(View view) { // NOSONAR S1172: XML onClick signature requires View.
        doneClicked = true;
        Intent data = new Intent()
            .putExtra(EXTRA_RF_POWER_HIGH, isHighPowerSelected())
            .putExtra(EXTRA_FREEDV_2400B_ENABLED, isFreeDv2400bSelected())
            .putExtra(EXTRA_BANDWIDTH, this.<AutoCompleteTextView>findViewById(R.id.bandwidthTextView).getText().toString().trim())
            .putExtra(EXTRA_SQUELCH, (int) this.<Slider>findViewById(R.id.squelchSlider).getValue())
            .putExtra(EXTRA_FILTER_PRE, this.<Switch>findViewById(R.id.emphasisSwitch).isChecked())
            .putExtra(EXTRA_FILTER_HIGH, this.<Switch>findViewById(R.id.highpassSwitch).isChecked())
            .putExtra(EXTRA_FILTER_LOW, this.<Switch>findViewById(R.id.lowpassSwitch).isChecked());
        setResult(Activity.RESULT_OK, data);
        finish();
    }

    private boolean isHighPowerSelected() {
        String[] powerOptions = getResources().getStringArray(R.array.rf_power_options);
        String selected = this.<AutoCompleteTextView>findViewById(R.id.rfPowerTextView).getText().toString().trim();
        return powerOptions.length == 0 || selected.equals(powerOptions[0]);
    }

    private boolean isFreeDv2400bSelected() {
        String[] voiceModeOptions = getResources().getStringArray(R.array.voice_mode_options);
        String selected = this.<AutoCompleteTextView>findViewById(R.id.voiceModeTextView).getText().toString().trim();
        return voiceModeOptions.length > 1 && selected.equals(voiceModeOptions[1]);
    }

    private void attachTextView(int viewId, Consumer<String> onTextChanged) {
        TextView view = findViewById(viewId);
        view.addTextChangedListener(new TextWatcher() {
            @Override public void beforeTextChanged(CharSequence s, int start, int count, int after) {
                // NOOP
            }
            @Override public void onTextChanged(CharSequence s, int start, int before, int count) {
                // NOOP
            }
            @Override public void afterTextChanged(Editable s) {
                onTextChanged.accept(s.toString().trim());
            }
        });
    }

    private String extractPrefix(String text) {
        return (text != null && text.length() >= 3) ? text.substring(0, 3) : text;
    }

    private void attachSwitch(int id, Consumer<Boolean> onChange) {
        ((Switch) findViewById(id)).setOnCheckedChangeListener((buttonView, isChecked) -> onChange.accept(isChecked));
    }

    private void attachListeners() {
        attachTextView(R.id.callsignTextInputEditText, text -> setCallsign(text.toUpperCase()));
        attachTextView(R.id.aprsPositionAccuracyTextView, this::setAprsPositionAccuracy);
        attachTextView(R.id.aprsIconTextView, this::setAprsIcon);
        attachTextView(R.id.aprsDestinationFilterTextView, this::setAprsDestinationFilter);
        attachTextView(R.id.min2mFreqTextView, text -> setMin2mTxFreq(extractPrefix(text)));
        attachTextView(R.id.max2mFreqTextView, text -> setMax2mTxFreq(extractPrefix(text)));
        attachTextView(R.id.min70cmFreqTextView, text -> setMin70cmTxFreq(extractPrefix(text)));
        attachTextView(R.id.max70cmFreqTextView, text -> setMax70cmTxFreq(extractPrefix(text)));
        attachTextView(R.id.micGainBoostTextView, this::setMicGainBoost);
        attachSwitch(R.id.stickyPTTSwitch, this::setStickyPTT);
        attachSwitch(R.id.noAnimationsSwitch, this::setNoAnimations);
        attachSwitch(R.id.aprsPositionSwitch, this::setAprsBeaconPosition);
        attachTextView(R.id.aprsBeaconFreqTextView, this::setAprsBeaconFrequency);
        attachSwitch(R.id.digipeatPacketsSwitch, this::setDigipeatPackets);
        attachSwitch(R.id.aprsIgateSwitch, this::setAprsIgate);
        attachSwitch(R.id.aprsIsDisplaySwitch, this::setAprsIsDisplay);
    }

    private void saveAppSettingAsync(String key, String value) {
        threadPoolExecutor.execute(() -> viewModel.getAppDb().saveAppSetting(key, value));
    }

    private void setAprsBeaconPosition(boolean enabled) {
        saveAppSettingAsync(AppSetting.SETTING_APRS_BEACON_POSITION, Boolean.toString(enabled));
        if (enabled && checkSelfPermission(Manifest.permission.ACCESS_FINE_LOCATION)
                != PackageManager.PERMISSION_GRANTED) {
            return;
        }
        if (radioAudioService != null) {
            radioAudioService.setAprsBeaconPosition(enabled);
        }
    }

    private void setAprsBeaconFrequency(String freq) {
        String frequency = freq;
        if (frequency.equals(getString(R.string.current))) {
            frequency = "Current";
        }
        saveAppSettingAsync(AppSetting.SETTING_APRS_BEACON_FREQUENCY, frequency);
        if (radioAudioService != null) {
            radioAudioService.setAprsBeaconFrequency(frequency);
        }
    }

    private void setAprsPositionAccuracy(String accuracy) {
        saveAppSettingAsync(AppSetting.SETTING_APRS_POSITION_ACCURACY, accuracy);
        if (radioAudioService != null) {
            radioAudioService.setAprsPositionAccuracy(accuracy.equals(getString(R.string.exact))
                ? RadioAudioService.APRS_POSITION_EXACT
                : RadioAudioService.APRS_POSITION_APPROX);
        }
    }

    private void setAprsIcon(String icon) {
        saveAppSettingAsync(AppSetting.SETTING_APRS_ICON, icon);
        if (radioAudioService != null) {
            radioAudioService.setAprsPositionIcon(getAPRSIconFromSettingChoice(getResources(), icon));
        }
    }

    private void setAprsDestinationFilter(String destinationFilter) {
        String value = getString(R.string.aprs_only_mine).equals(destinationFilter)
            ? AprsFeedPolicy.DESTINATION_MINE : AprsFeedPolicy.DESTINATION_ALL;
        saveAppSettingAsync(AppSetting.SETTING_APRS_DESTINATION_FILTER, value);
        if (radioAudioService != null) {
            radioAudioService.setAprsDestinationFilter(value);
        }
    }

    private void setAprsIgate(boolean enabled) {
        saveAppSettingAsync(AppSetting.SETTING_APRS_IGATE, Boolean.toString(enabled));
        if (radioAudioService != null) radioAudioService.setAprsIgateEnabled(enabled);
    }

    private void setAprsIsDisplay(boolean enabled) {
        saveAppSettingAsync(AppSetting.SETTING_APRS_IS_DISPLAY, Boolean.toString(enabled));
        if (radioAudioService != null) radioAudioService.setAprsIsDisplayEnabled(enabled);
    }

    private void setMin2mTxFreq(String freq) {
        saveAppSettingAsync(AppSetting.SETTING_MIN_2_M_TX_FREQ, freq);
    }

    private void setMax2mTxFreq(String freq) {
        saveAppSettingAsync(AppSetting.SETTING_MAX_2_M_TX_FREQ, freq);
    }

    private void setMin70cmTxFreq(String freq) {
        saveAppSettingAsync(AppSetting.SETTING_MIN_70_CM_TX_FREQ, freq);
    }

    private void setMax70cmTxFreq(String freq) {
        saveAppSettingAsync(AppSetting.SETTING_MAX_70_CM_TX_FREQ, freq);
    }

    private void setMicGainBoost(String level) {
        saveAppSettingAsync(AppSetting.SETTING_MIC_GAIN_BOOST, level);
    }

    private void setCallsign(String callsign) {
        saveAppSettingAsync(AppSetting.SETTING_CALLSIGN, callsign);
    }

    private void setStickyPTT(boolean enabled) {
        saveAppSettingAsync(AppSetting.SETTING_STICKY_PTT, Boolean.toString(enabled));
    }

    private void setNoAnimations(boolean enabled) {
        saveAppSettingAsync(AppSetting.SETTING_DISABLE_ANIMATIONS, Boolean.toString(enabled));
    }

    private void setDigipeatPackets(boolean enabled) {
        saveAppSettingAsync(AppSetting.SETTING_DIGIPEAT_PACKETS, Boolean.toString(enabled));
        if (radioAudioService != null) {
            radioAudioService.setDigipeatPackets(enabled);
        }
    }

    public static APRSIconType getAPRSIconFromSettingChoice(Resources resources, String choice) {
        if (choice != null) {
            for (int i = 0; i < APRS_ICON_CHOICE_RESOURCES.length; i++) {
                if (resources.getString(APRS_ICON_CHOICE_RESOURCES[i]).equals(choice)) {
                    return APRS_ICON_TYPES[i];
                }
            }
        }
        return APRSIconType.T_PHONE;
    }
}
